hcen1997/pixel-bean/audiuno-code/IMG_20260302_231758.jpg

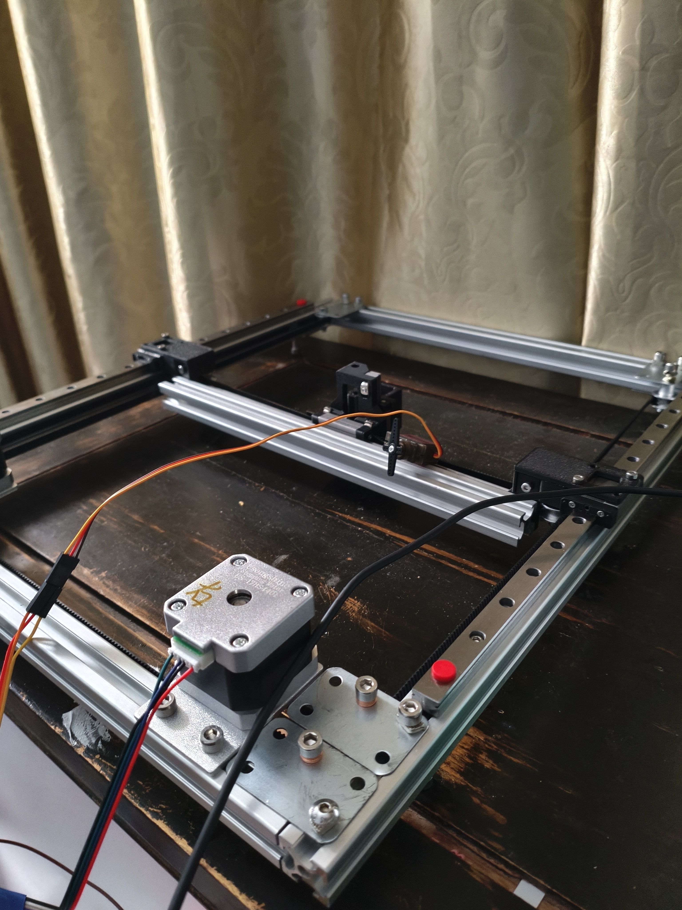
audiuno-code/IMG_20260302_231758.jpg
