hcen1997/pixel-bean/audiuno-code/IMG_20260302_231801.jpg

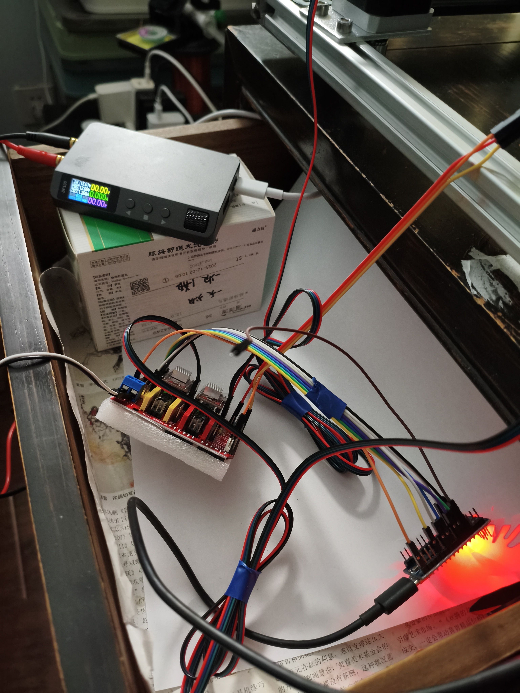
audiuno-code/IMG_20260302_231801.jpg
