hcen1997/pixel-bean/audiuno-code/IMG_20260304_140346.jpg

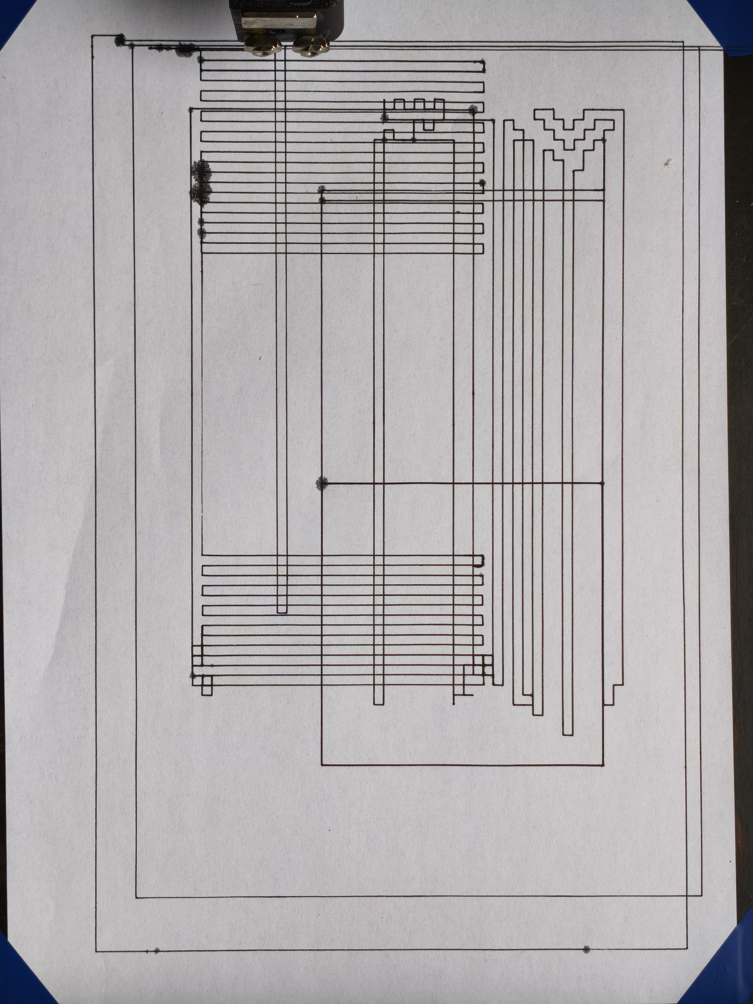
audiuno-code/IMG_20260304_140346.jpg
