hcen1997/pixel-bean/audiuno-code/taobao-doc/c99ceb875f869f8083b27c238d63576b.png

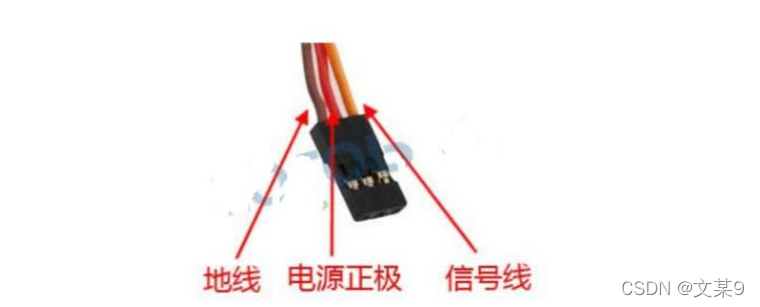
audiuno-code/taobao-doc/c99ceb875f869f8083b27c238d63576b.png
