hcen1997/pixel-bean/audiuno-code/taobao-doc/Screenshot_2026-02-28-11-37-00-495_com.taobao.tao.jpg

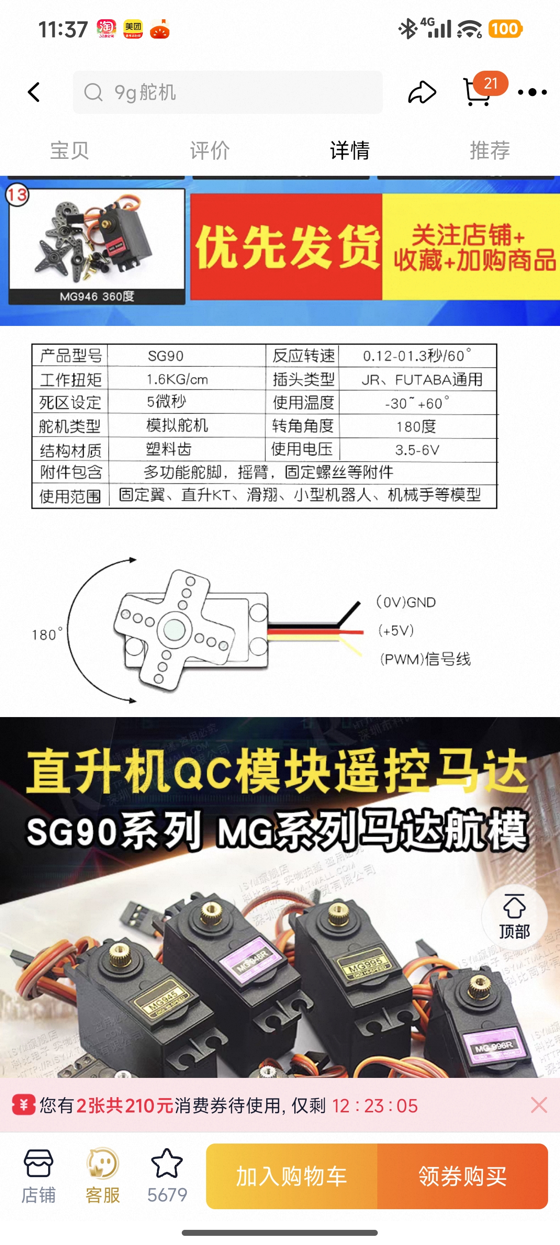
audiuno-code/taobao-doc/Screenshot_2026-02-28-11-37-00-495_com.taobao.tao.jpg
