hcen1997/pixel-bean/audiuno-code/taobao-doc/Screenshot_2026-02-28-11-39-15-636_com.taobao.tao.jpg

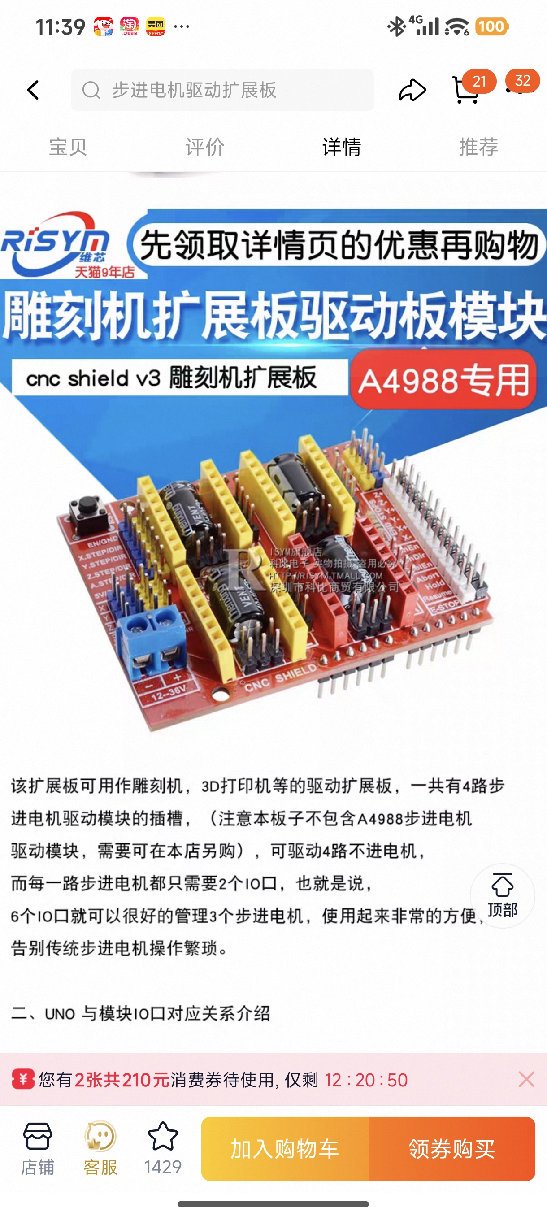
audiuno-code/taobao-doc/Screenshot_2026-02-28-11-39-15-636_com.taobao.tao.jpg
