hcen1997/pixel-bean/audiuno-code/taobao-doc/Screenshot_2026-02-28-11-39-21-068_com.taobao.tao.jpg

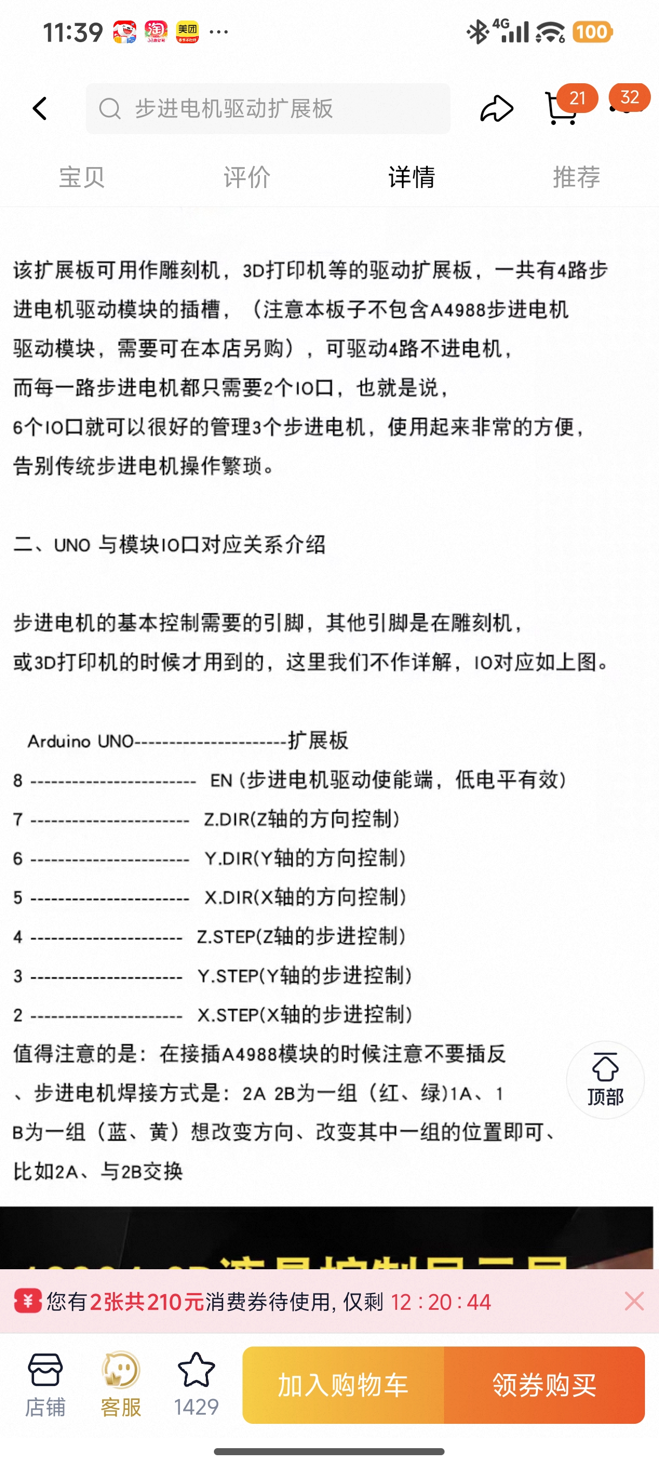
audiuno-code/taobao-doc/Screenshot_2026-02-28-11-39-21-068_com.taobao.tao.jpg
