hcen1997/pixel-bean/grbl-code/0c6dcc0a55ac43939d65316e1c08b687.jpeg~tplv-a9rns2rl98-image.jpg

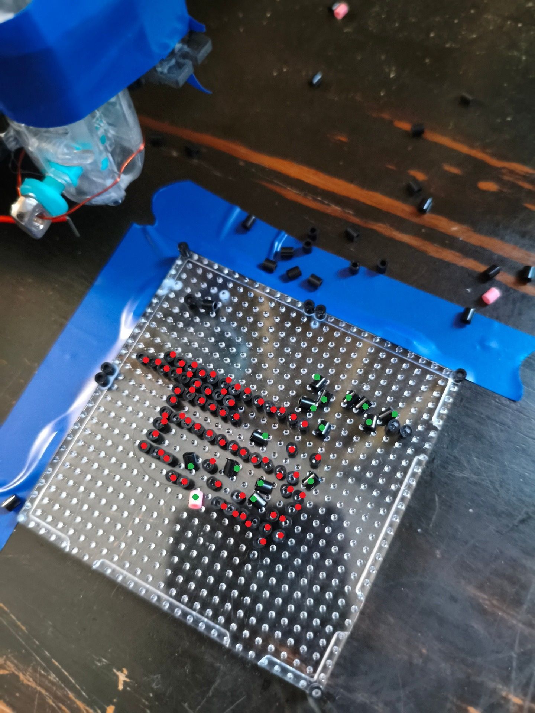
grbl-code/0c6dcc0a55ac43939d65316e1c08b687.jpeg~tplv-a9rns2rl98-image.jpg
