hcen1997/pixel-bean/grbl-code/IMG_20260304_173114.jpg

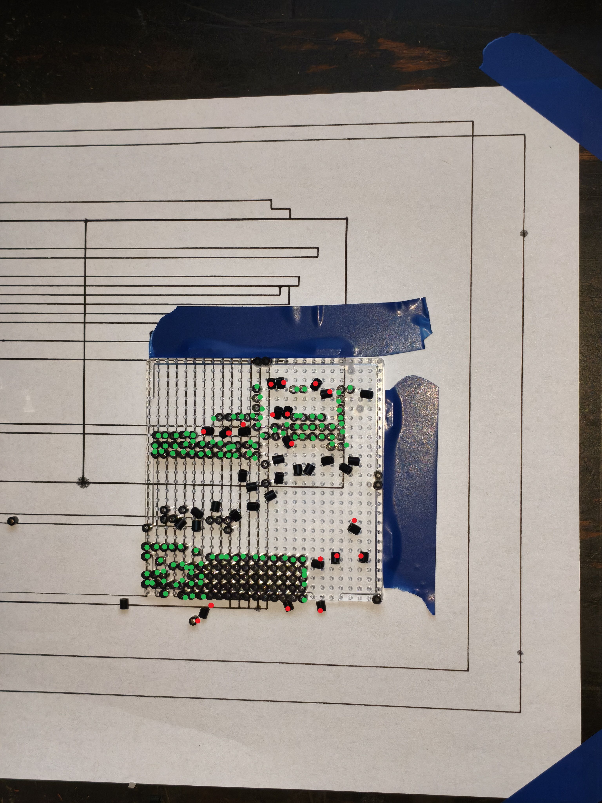
grbl-code/IMG_20260304_173114.jpg
