hcen1997/pixel-bean/grbl-code/pattern-mard-1772532473487.jpg

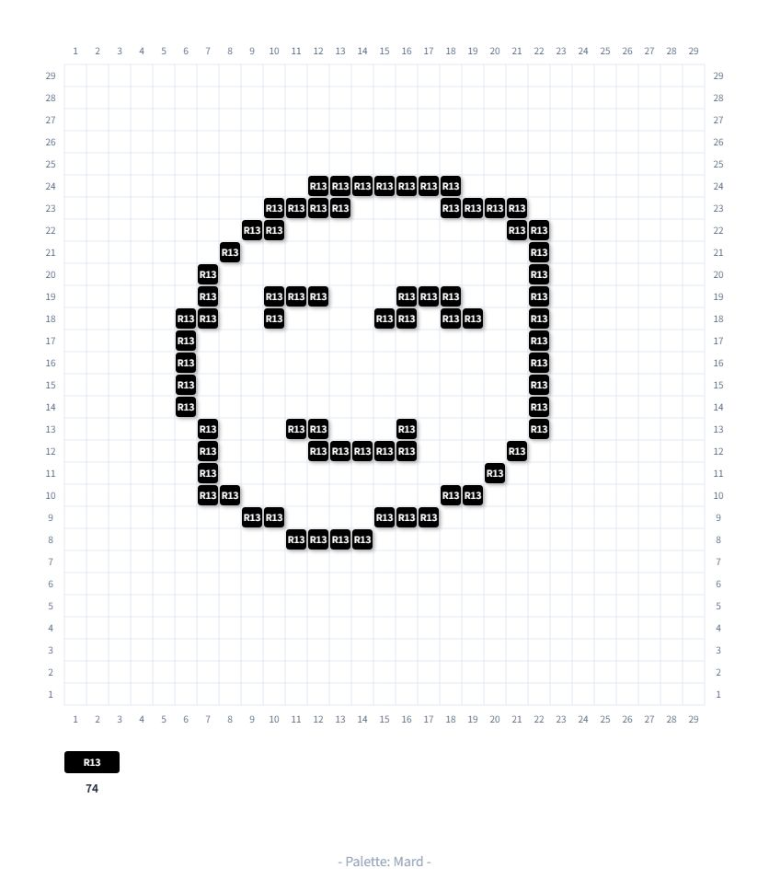
grbl-code/pattern-mard-1772532473487.jpg
