hcen1997/pixel-bean/video_analsys/frames/0001.jpg

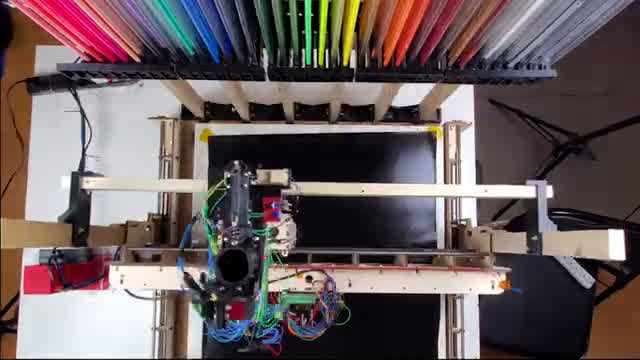
video_analsys/frames/0001.jpg
