hcen1997/pixel-bean/video_analsys/frames/0002.jpg

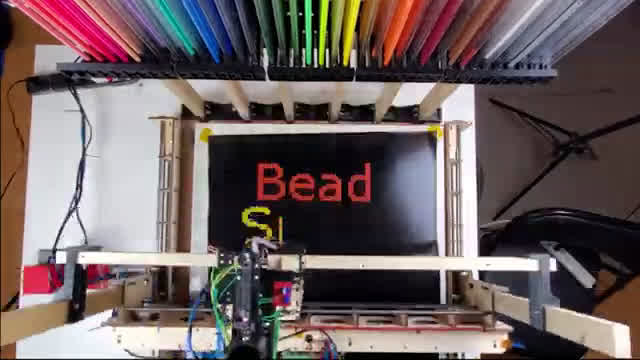
video_analsys/frames/0002.jpg
