hcen1997/pixel-bean/video_analsys/frames/0003.jpg

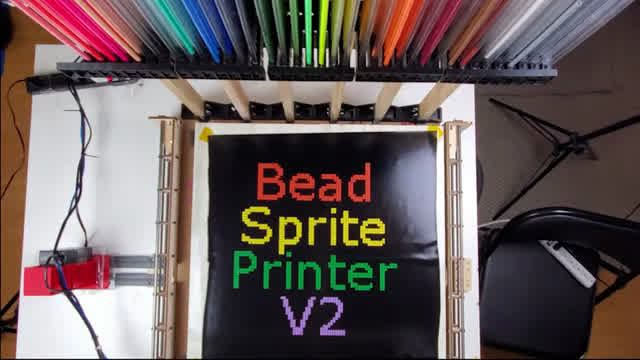
video_analsys/frames/0003.jpg
