hcen1997/pixel-bean/video_analsys/frames/0004.jpg

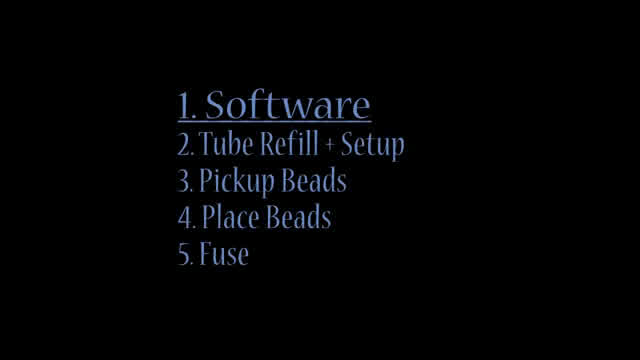
video_analsys/frames/0004.jpg
