hcen1997/pixel-bean/video_analsys/frames/0005.jpg

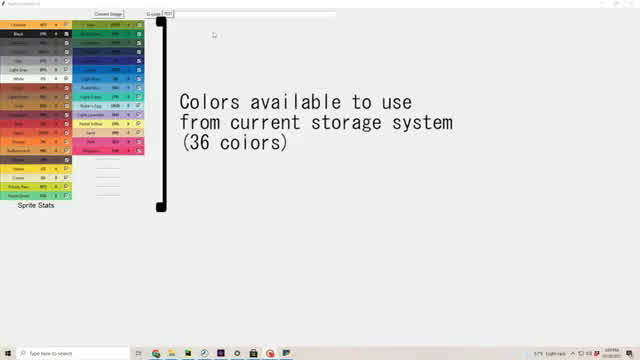
video_analsys/frames/0005.jpg
