hcen1997/pixel-bean/video_analsys/frames/0006.jpg

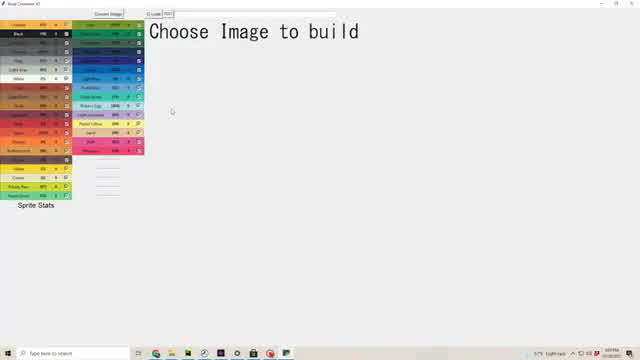
video_analsys/frames/0006.jpg
