hcen1997/pixel-bean/video_analsys/frames/0007.jpg

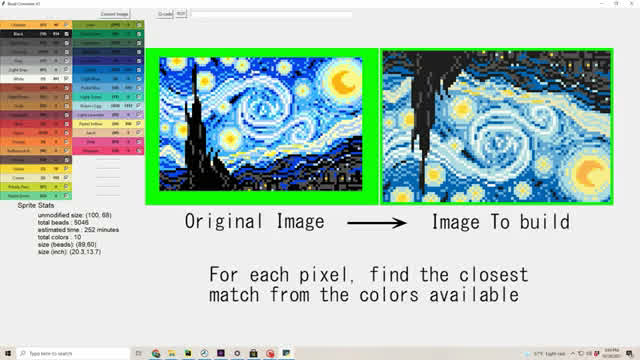
video_analsys/frames/0007.jpg
