hcen1997/pixel-bean/video_analsys/frames/0009.jpg

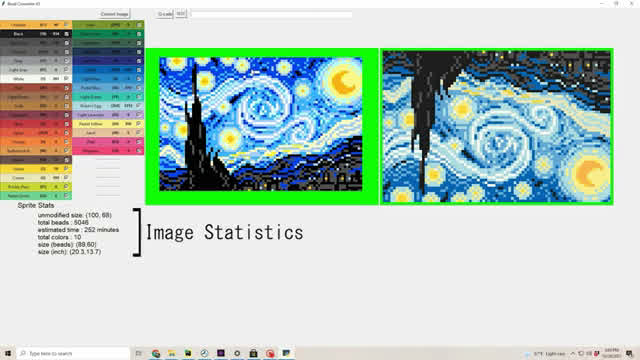
video_analsys/frames/0009.jpg
