hcen1997/pixel-bean/video_analsys/frames/0010.jpg

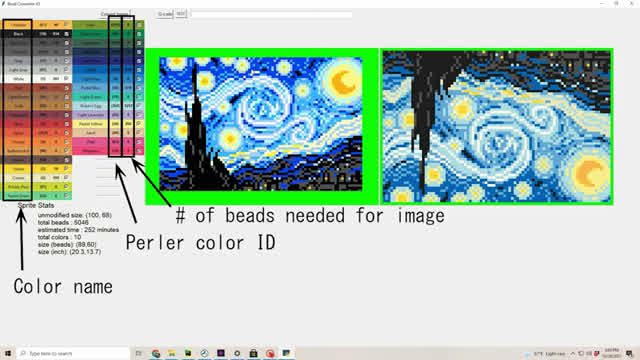
video_analsys/frames/0010.jpg
