hcen1997/pixel-bean/video_analsys/frames/0011.jpg

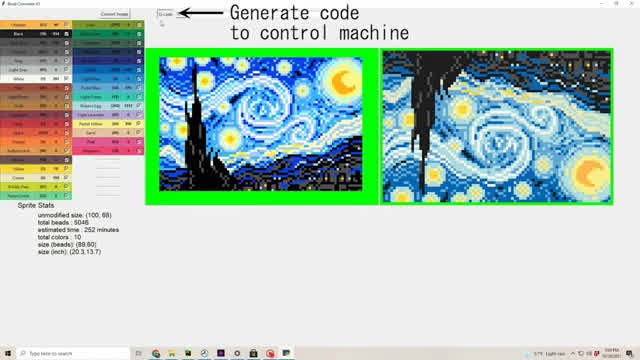
video_analsys/frames/0011.jpg
