hcen1997/pixel-bean/video_analsys/frames/0013.jpg

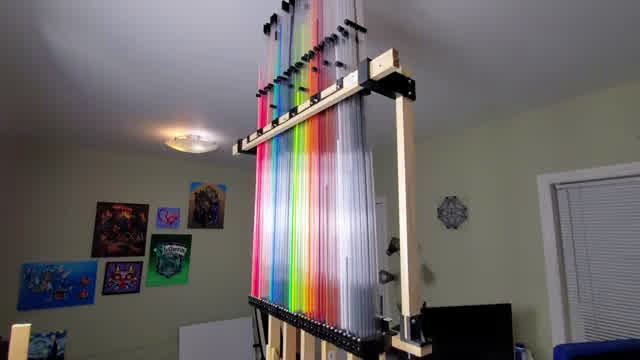
video_analsys/frames/0013.jpg
