hcen1997/pixel-bean/video_analsys/frames/0014.jpg

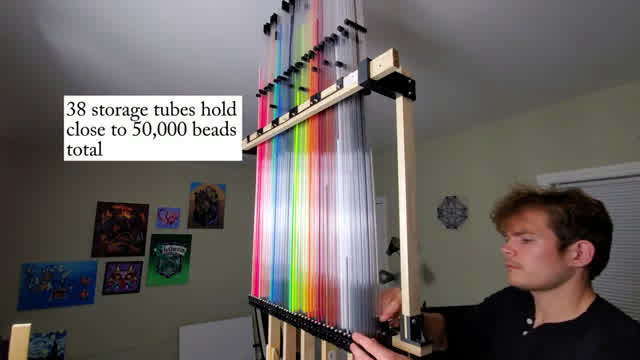
video_analsys/frames/0014.jpg
