hcen1997/pixel-bean/video_analsys/frames/0015.jpg

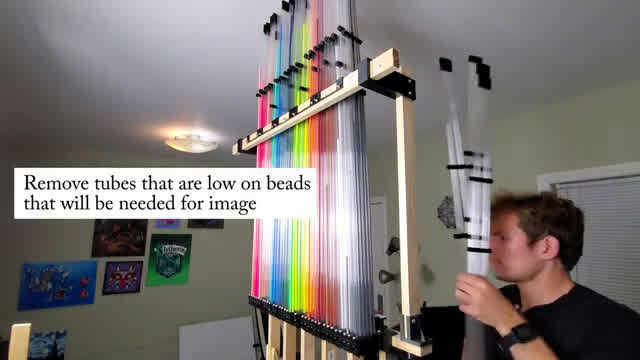
video_analsys/frames/0015.jpg
