hcen1997/pixel-bean/video_analsys/frames/0016.jpg

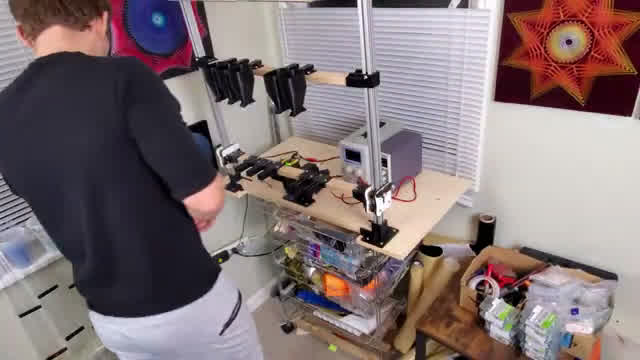
video_analsys/frames/0016.jpg
