hcen1997/pixel-bean/video_analsys/frames/0017.jpg

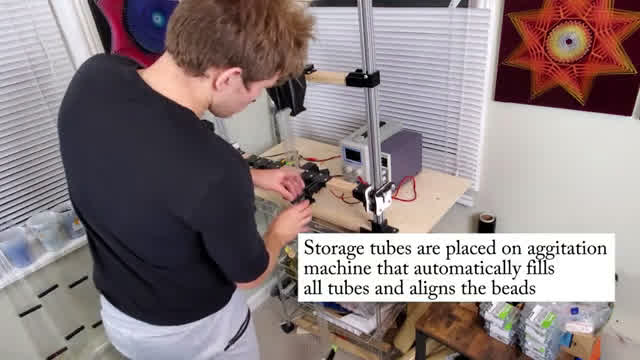
video_analsys/frames/0017.jpg
