hcen1997/pixel-bean/video_analsys/frames/0018.jpg

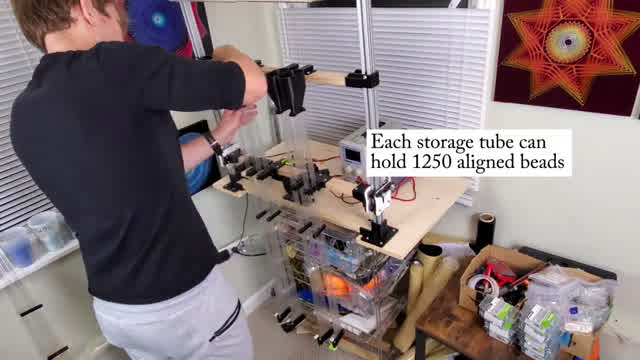
video_analsys/frames/0018.jpg
