hcen1997/pixel-bean/video_analsys/frames/0019.jpg

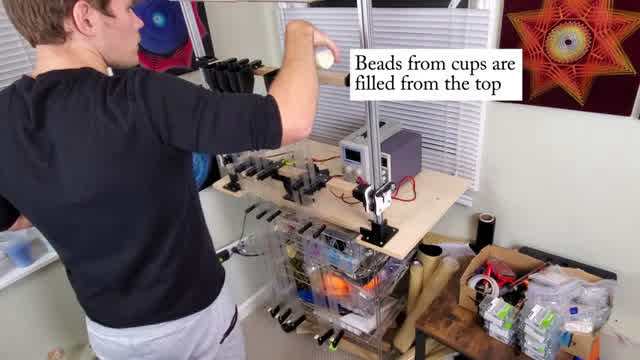
video_analsys/frames/0019.jpg
