hcen1997/pixel-bean/video_analsys/frames/0020.jpg

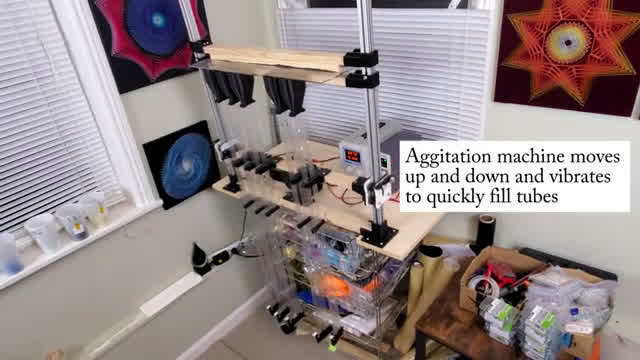
video_analsys/frames/0020.jpg
