hcen1997/pixel-bean/video_analsys/frames/0021.jpg

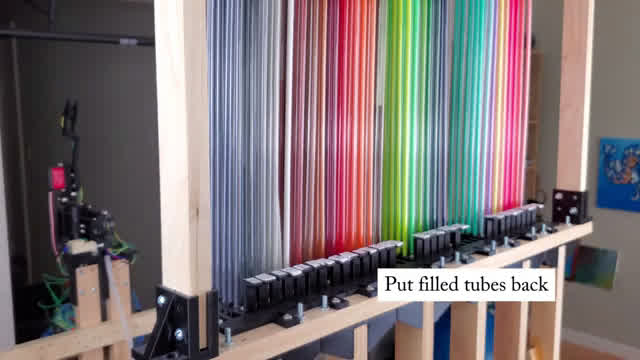
video_analsys/frames/0021.jpg
