hcen1997/pixel-bean/video_analsys/frames/0022.jpg

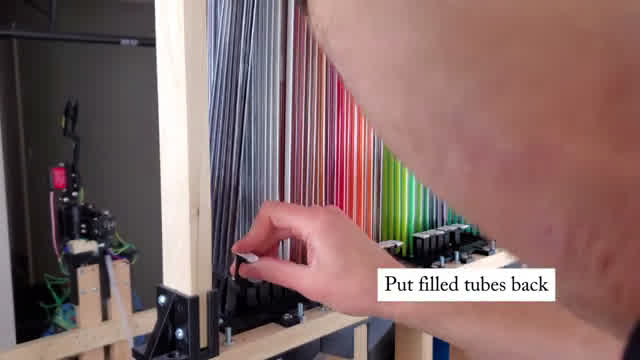
video_analsys/frames/0022.jpg
