hcen1997/pixel-bean/video_analsys/frames/0024.jpg

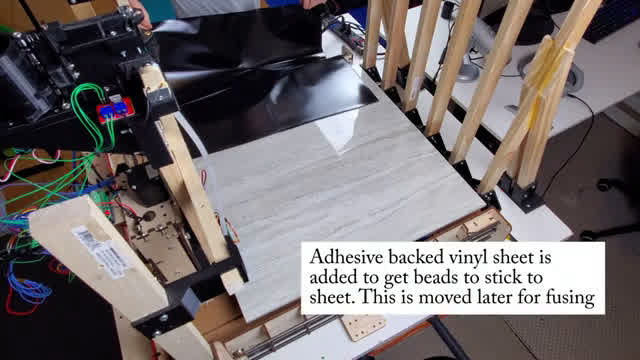
video_analsys/frames/0024.jpg
