hcen1997/pixel-bean/video_analsys/frames/0026.jpg

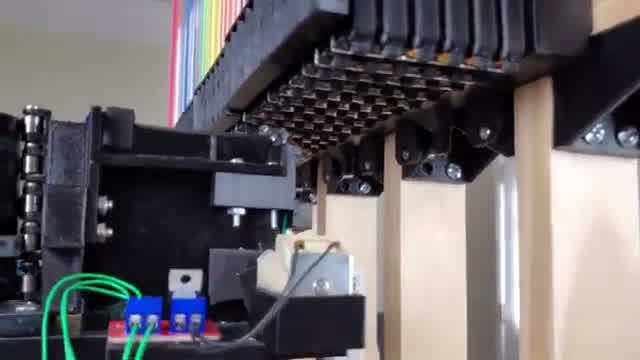
video_analsys/frames/0026.jpg
