hcen1997/pixel-bean/video_analsys/frames/0027.jpg

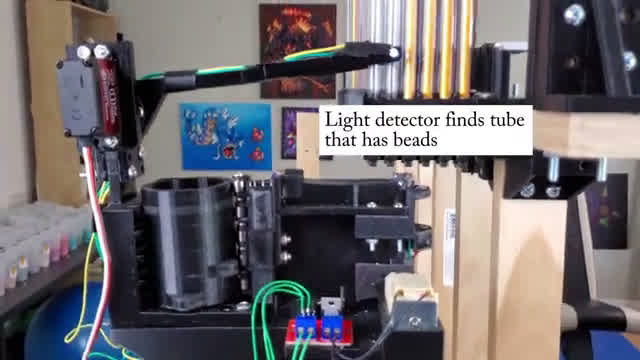
video_analsys/frames/0027.jpg
