hcen1997/pixel-bean/video_analsys/frames/0028.jpg

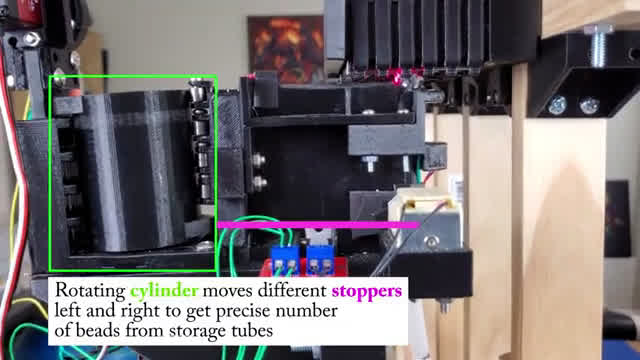
video_analsys/frames/0028.jpg
