hcen1997/pixel-bean/video_analsys/frames/0029.jpg

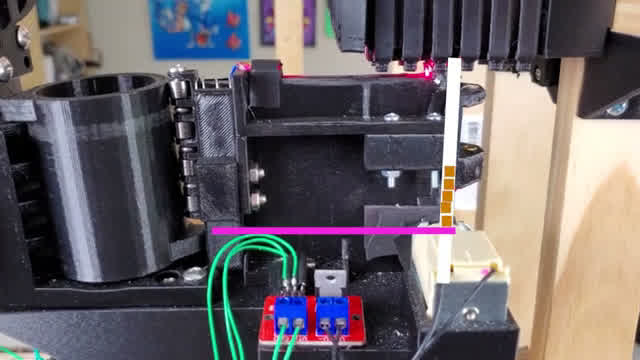
video_analsys/frames/0029.jpg
