hcen1997/pixel-bean/video_analsys/frames/0030.jpg

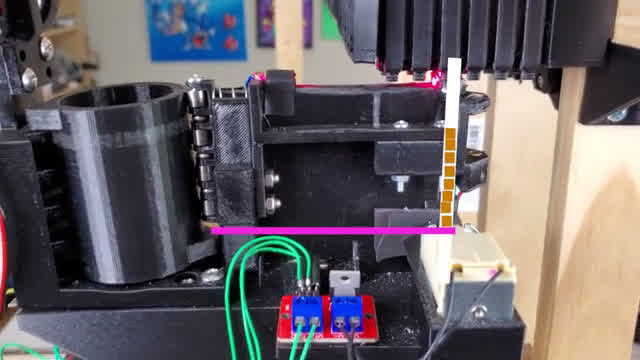
video_analsys/frames/0030.jpg
