hcen1997/pixel-bean/video_analsys/frames/0031.jpg

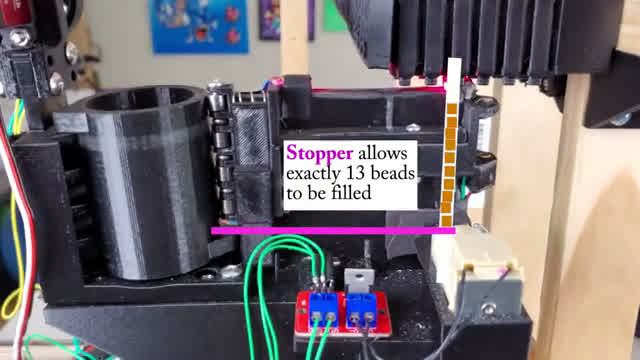
video_analsys/frames/0031.jpg
