hcen1997/pixel-bean/video_analsys/frames/0032.jpg

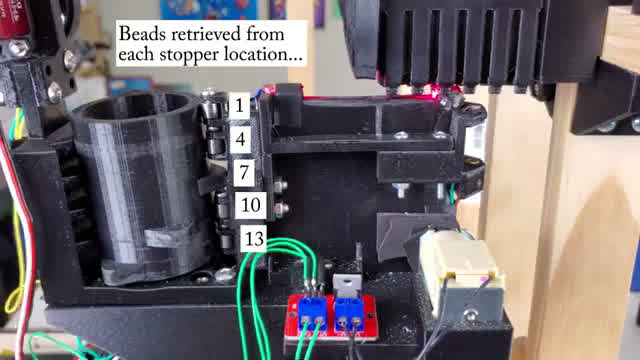
video_analsys/frames/0032.jpg
