hcen1997/pixel-bean/video_analsys/frames/0033.jpg

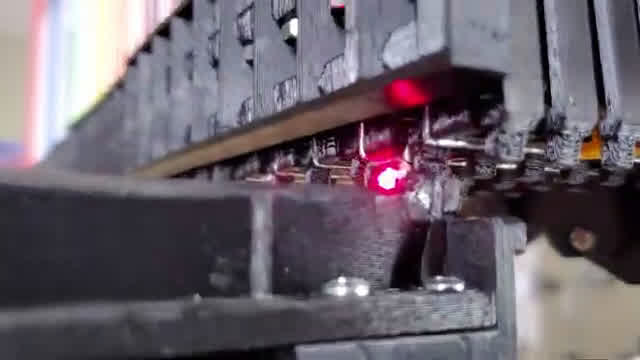
video_analsys/frames/0033.jpg
