hcen1997/pixel-bean/video_analsys/frames/0034.jpg

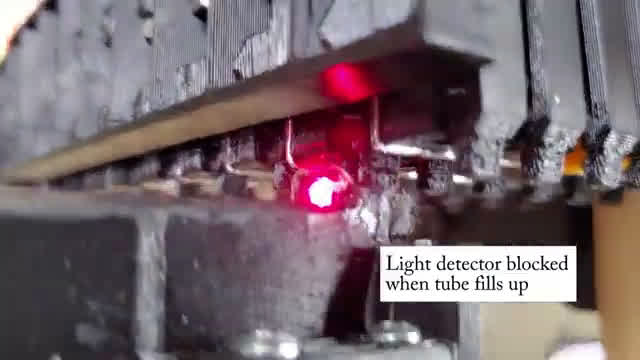
video_analsys/frames/0034.jpg
