hcen1997/pixel-bean/video_analsys/frames/0035.jpg

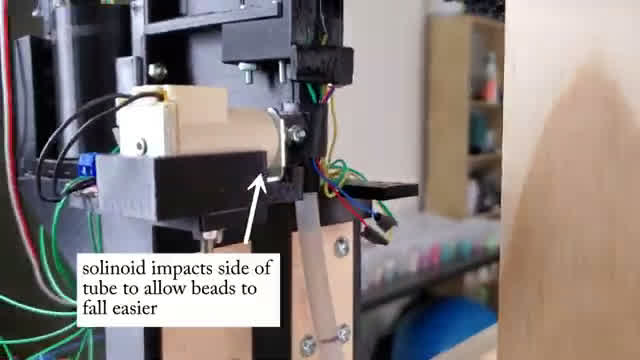
video_analsys/frames/0035.jpg
