hcen1997/pixel-bean/video_analsys/frames/0037.jpg

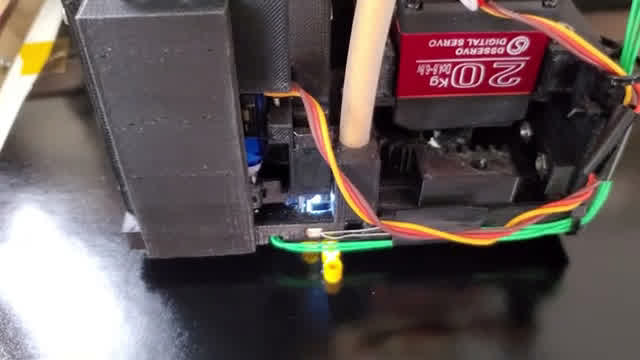
video_analsys/frames/0037.jpg
