hcen1997/pixel-bean/video_analsys/frames/0038.jpg

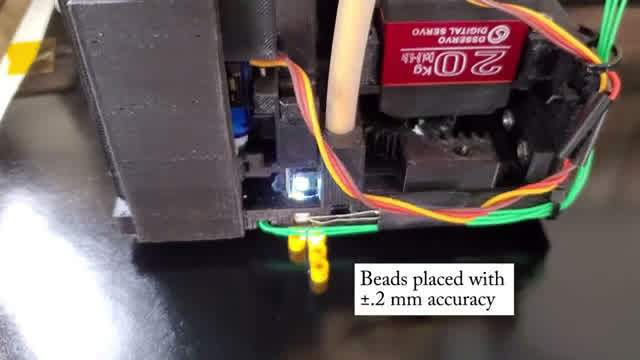
video_analsys/frames/0038.jpg
