hcen1997/pixel-bean/video_analsys/frames/0039.jpg

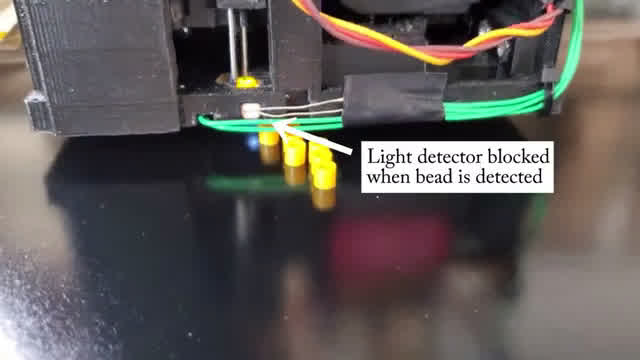
video_analsys/frames/0039.jpg
