hcen1997/pixel-bean/video_analsys/frames/0040.jpg

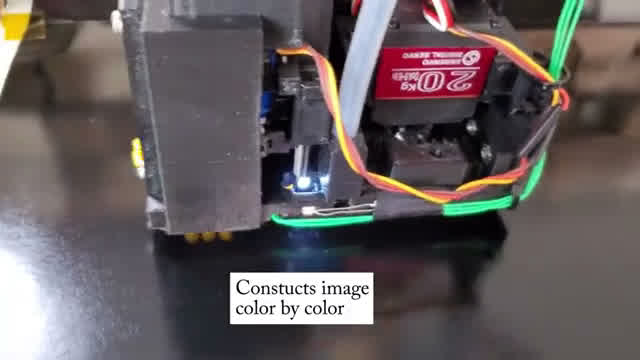
video_analsys/frames/0040.jpg
