hcen1997/pixel-bean/video_analsys/frames/0041.jpg

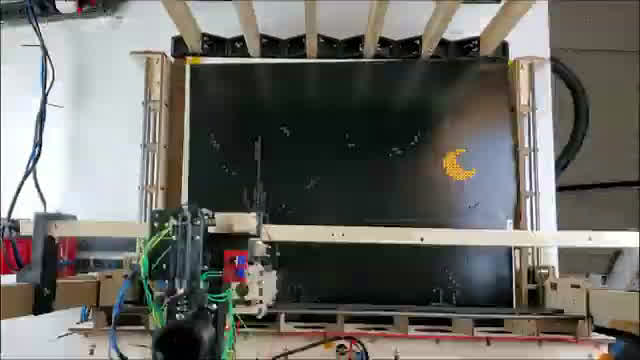
video_analsys/frames/0041.jpg
