hcen1997/pixel-bean/video_analsys/frames/0042.jpg

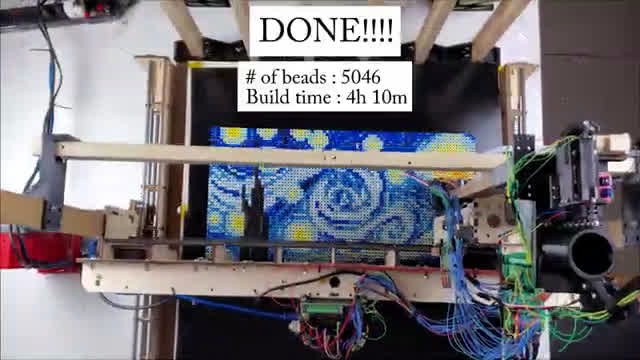
video_analsys/frames/0042.jpg
