hcen1997/pixel-bean/video_analsys/frames/0043.jpg

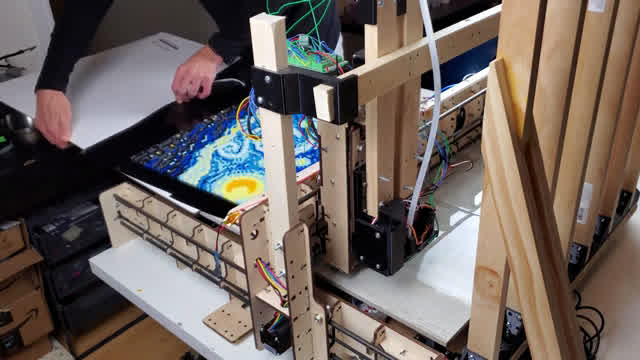
video_analsys/frames/0043.jpg
