hcen1997/pixel-bean/video_analsys/frames/0044.jpg

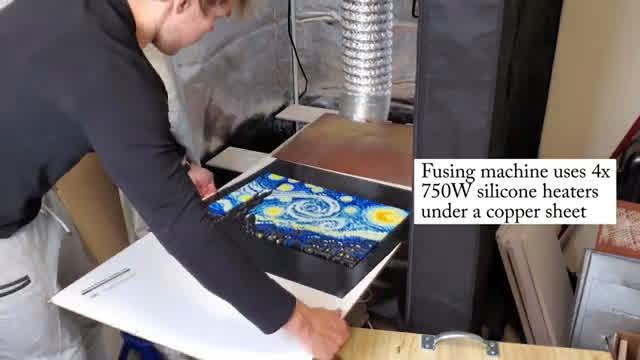
video_analsys/frames/0044.jpg
