hcen1997/pixel-bean/video_analsys/frames/0045.jpg

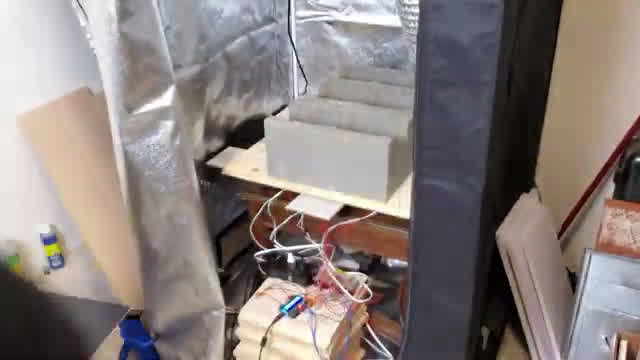
video_analsys/frames/0045.jpg
