hcen1997/pixel-bean/video_analsys/frames/0046.jpg

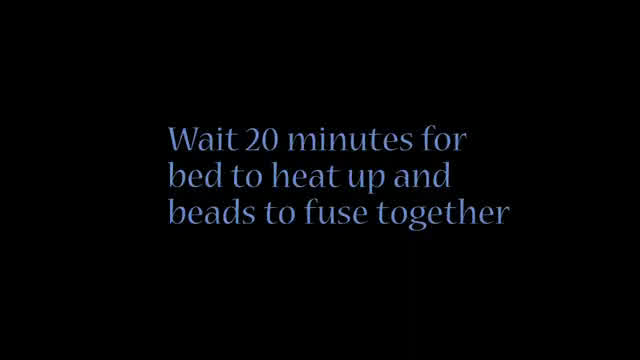
video_analsys/frames/0046.jpg
