hcen1997/pixel-bean/video_analsys/frames/0047.jpg

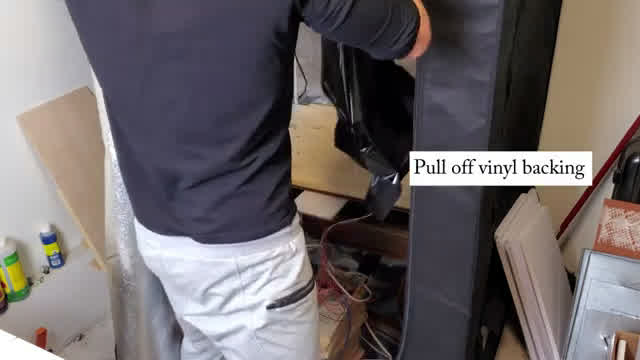
video_analsys/frames/0047.jpg
