hcen1997/pixel-bean/video_analsys/frames/0048.jpg

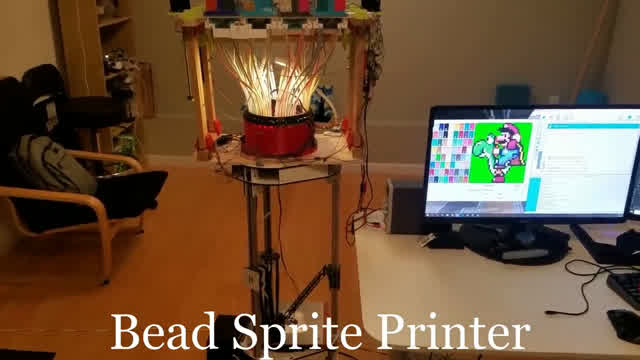
video_analsys/frames/0048.jpg
