hcen1997/pixel-bean/video_analsys/frames/0049.jpg

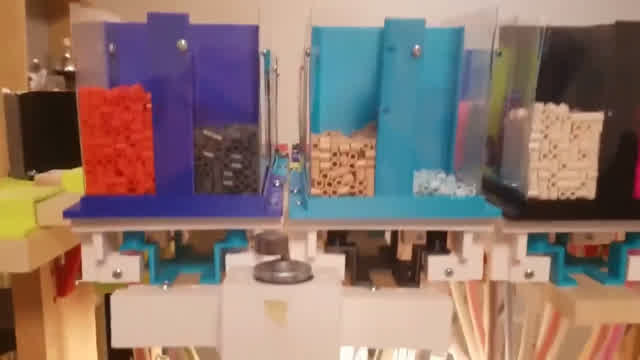
video_analsys/frames/0049.jpg
