hcen1997/pixel-bean/video_analsys/frames/0050.jpg

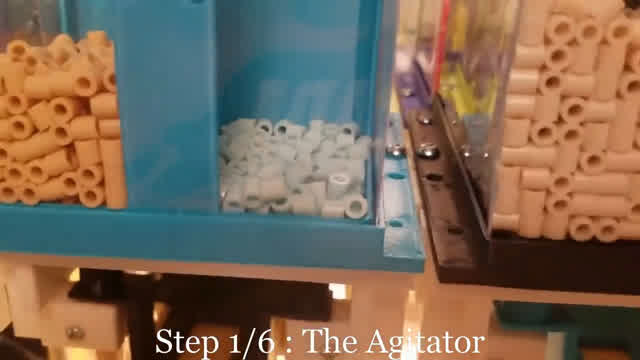
video_analsys/frames/0050.jpg
