hcen1997/pixel-bean/video_analsys/frames/0051.jpg

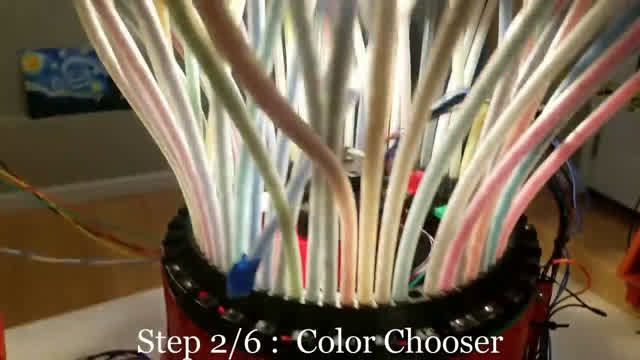
video_analsys/frames/0051.jpg
