hcen1997/pixel-bean/video_analsys/frames/0052.jpg

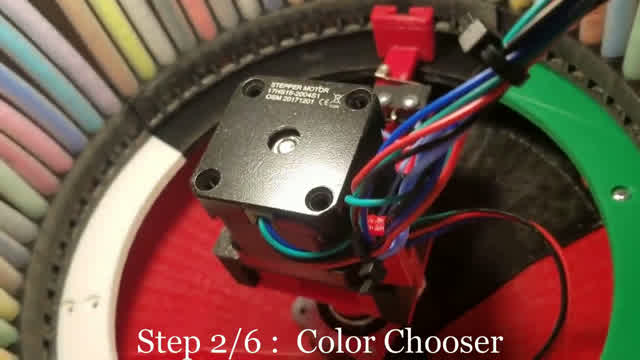
video_analsys/frames/0052.jpg
