hcen1997/pixel-bean/video_analsys/frames/0053.jpg

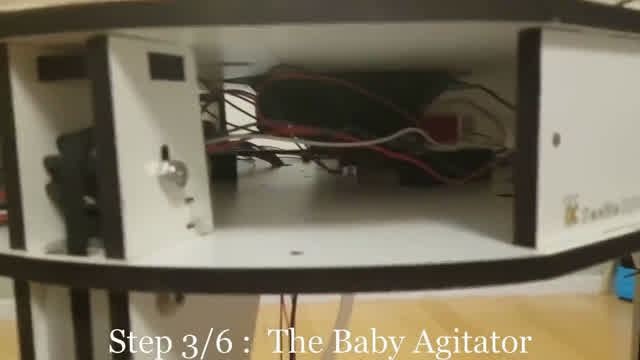
video_analsys/frames/0053.jpg
