hcen1997/pixel-bean/video_analsys/frames/0054.jpg

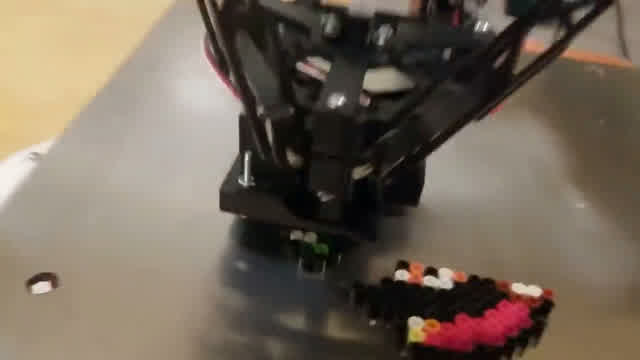
video_analsys/frames/0054.jpg
