hcen1997/pixel-bean/video_analsys/frames/0055.jpg

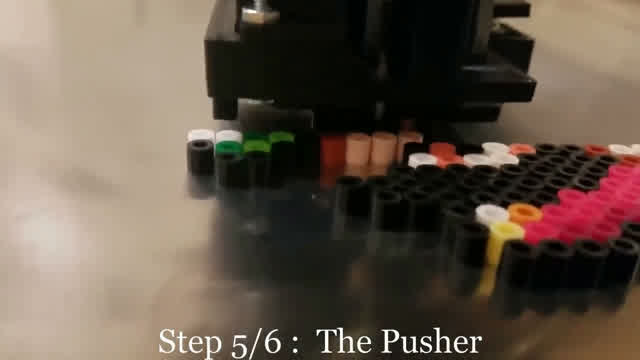
video_analsys/frames/0055.jpg
