hcen1997/pixel-bean/video_analsys/frames/0056.jpg

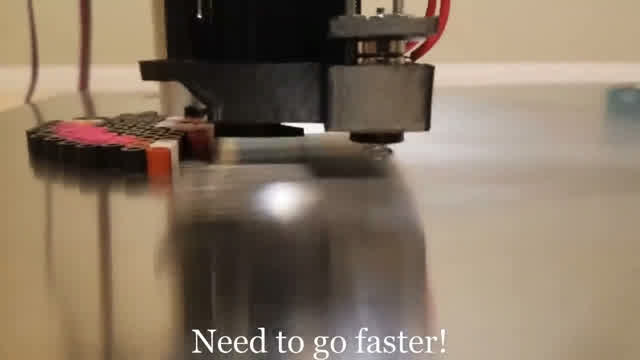
video_analsys/frames/0056.jpg
