hcen1997/pixel-bean/video_analsys/frames/0057.jpg

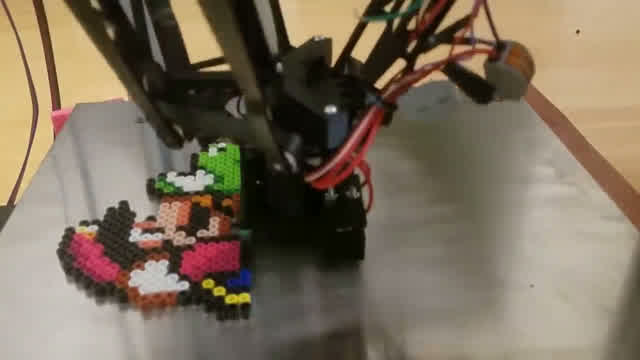
video_analsys/frames/0057.jpg
