hcen1997/pixel-bean/video_analsys/frames/0058.jpg

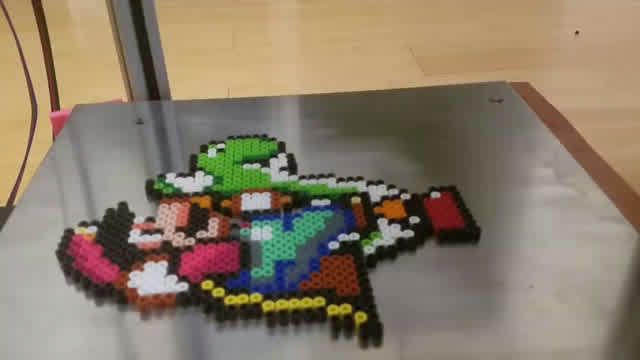
video_analsys/frames/0058.jpg
