hcen1997/pixel-bean/video_analsys/frames/0060.jpg

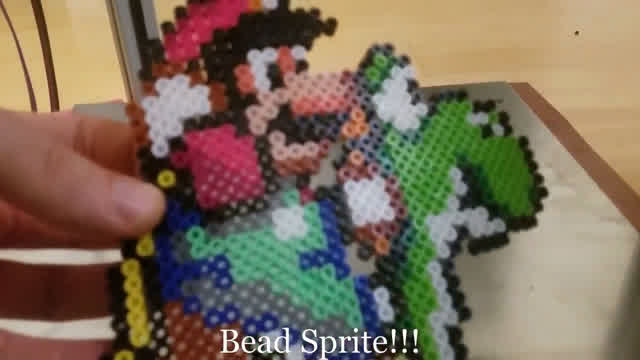
video_analsys/frames/0060.jpg
