hcen1997/pixel-bean/video_analsys/frames/0061.jpg

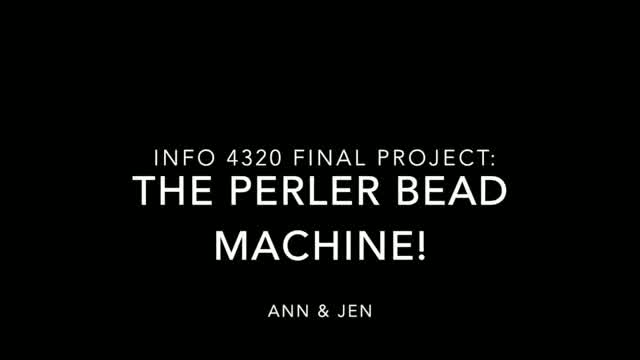
video_analsys/frames/0061.jpg
