hcen1997/pixel-bean/video_analsys/frames/0062.jpg

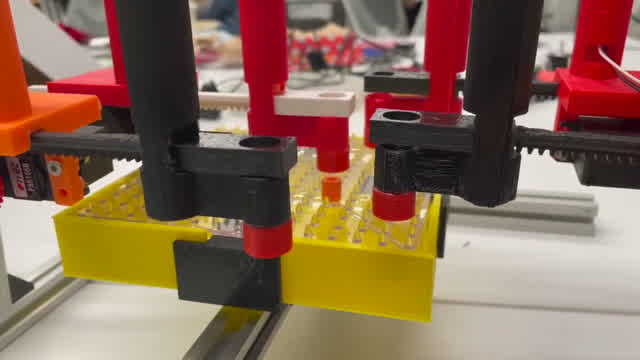
video_analsys/frames/0062.jpg
