hcen1997/pixel-bean/video_analsys/frames/0063.jpg

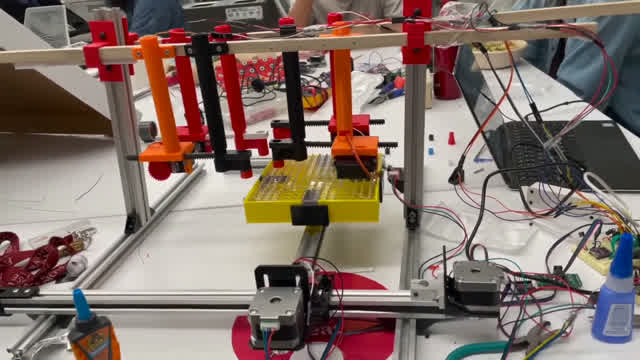
video_analsys/frames/0063.jpg
