hcen1997/pixel-bean/video_analsys/frames/0064.jpg

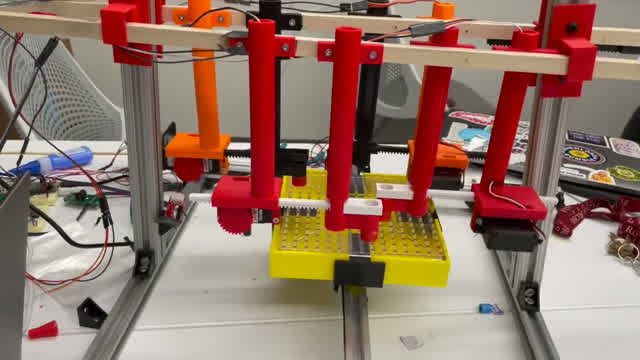
video_analsys/frames/0064.jpg
