hcen1997/pixel-bean/video_analsys/frames/0065.jpg

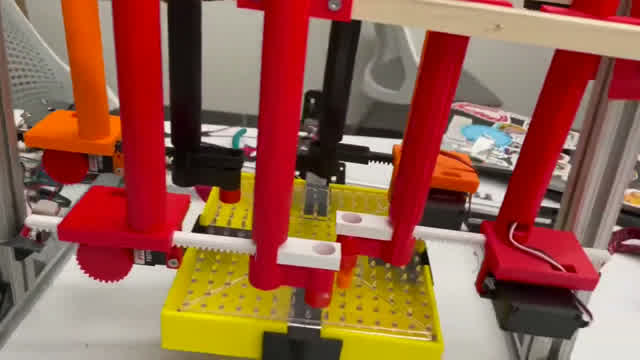
video_analsys/frames/0065.jpg
