hcen1997/pixel-bean/video_analsys/frames/0067.jpg

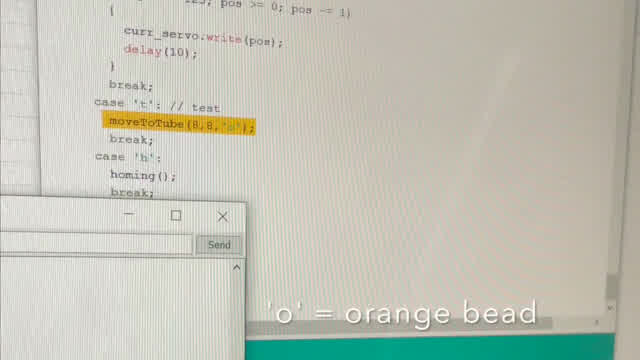
video_analsys/frames/0067.jpg
