hcen1997/pixel-bean/video_analsys/frames/0068.jpg

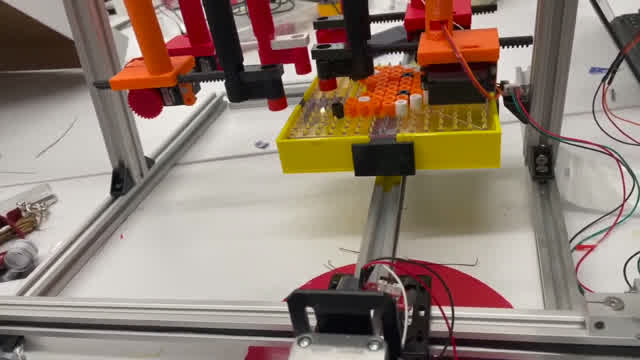
video_analsys/frames/0068.jpg
