hcen1997/pixel-bean/video_analsys/frames/0069.jpg

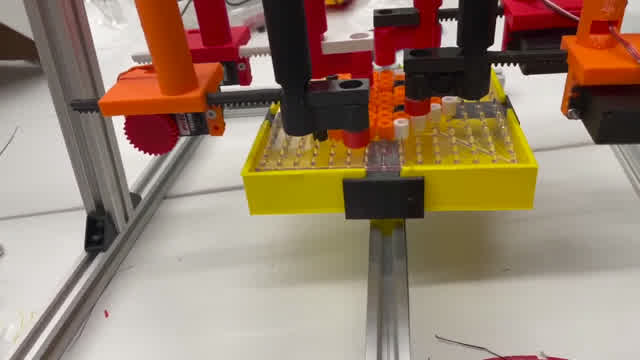
video_analsys/frames/0069.jpg
