hcen1997/pixel-bean/video_analsys/frames/0070.jpg

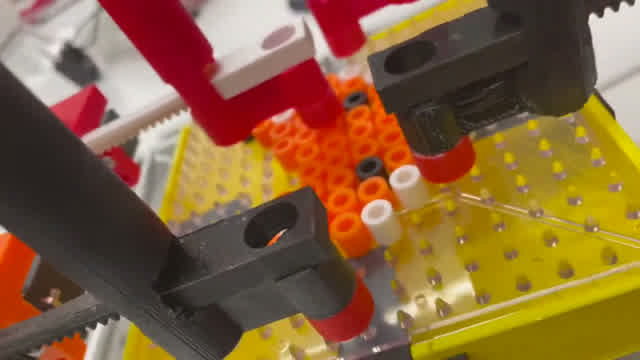
video_analsys/frames/0070.jpg
