hcen1997/pixel-bean/video_analsys/frames/0071.jpg

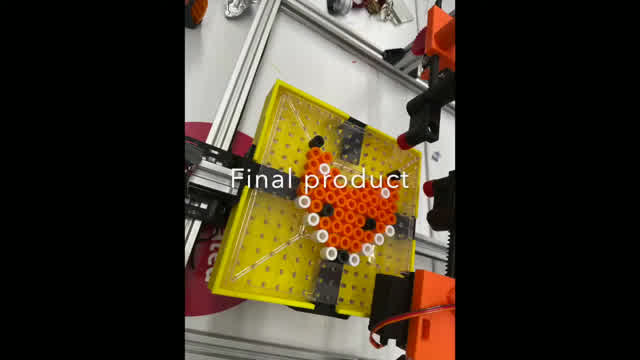
video_analsys/frames/0071.jpg
