hcen1997/pixel-bean/video_analsys/frames/0072.jpg

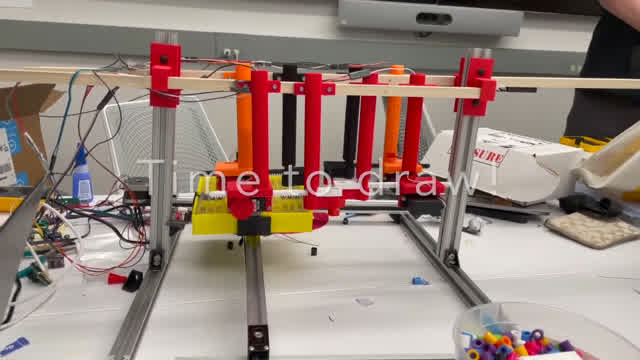
video_analsys/frames/0072.jpg
