hcen1997/pixel-bean/video_analsys/frames/0073.jpg

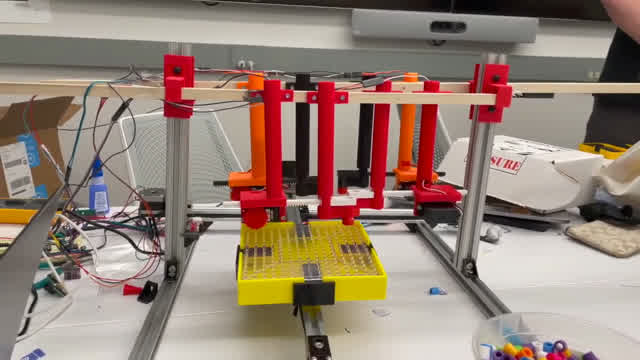
video_analsys/frames/0073.jpg
