hcen1997/pixel-bean/video_analsys/frames/0074.jpg

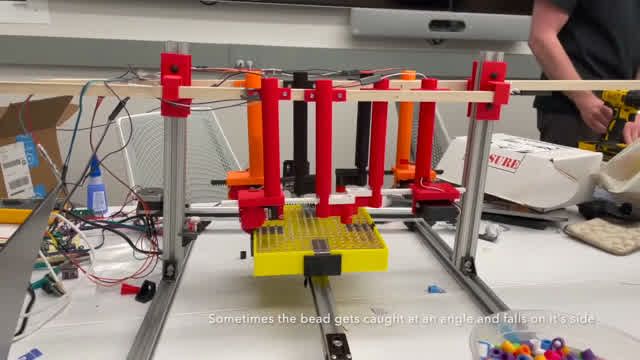
video_analsys/frames/0074.jpg
