hcen1997/pixel-bean/video_analsys/frames/0075.jpg

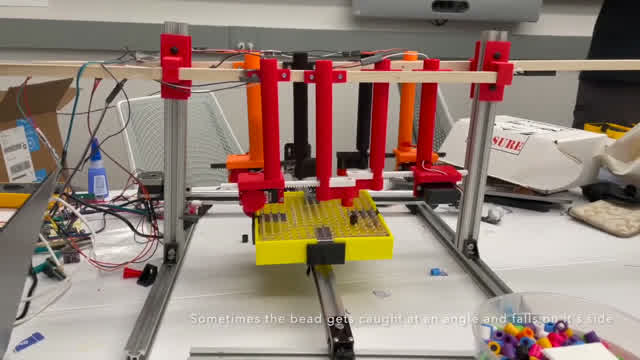
video_analsys/frames/0075.jpg
