hcen1997/pixel-bean/video_analsys/frames/0076.jpg

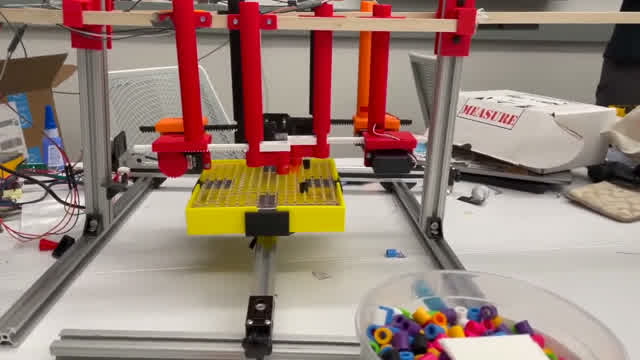
video_analsys/frames/0076.jpg
