hcen1997/pixel-bean/video_analsys/frames/0077.jpg

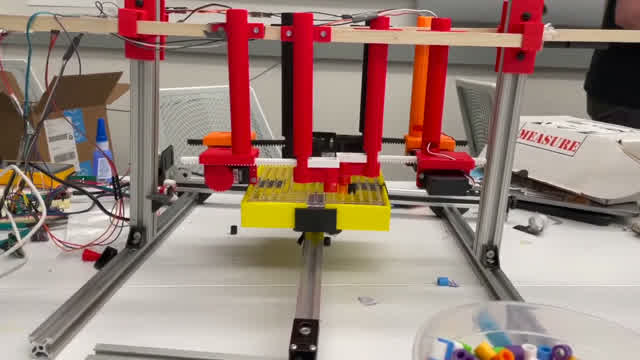
video_analsys/frames/0077.jpg
