hcen1997/pixel-bean/video_analsys/frames/0078.jpg

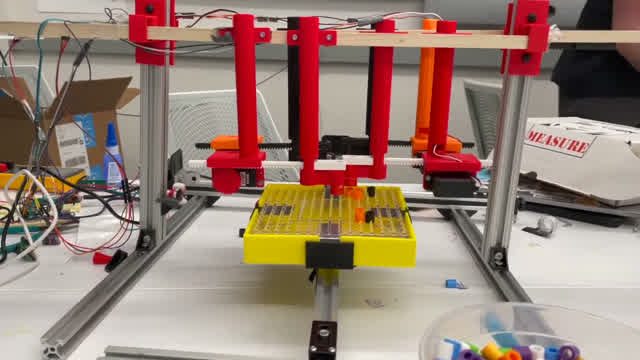
video_analsys/frames/0078.jpg
