hcen1997/pixel-bean/video_analsys/frames/0079.jpg

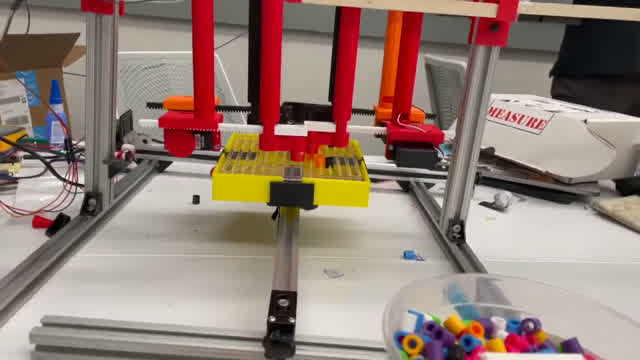
video_analsys/frames/0079.jpg
