hcen1997/pixel-bean/video_analsys/frames/0080.jpg

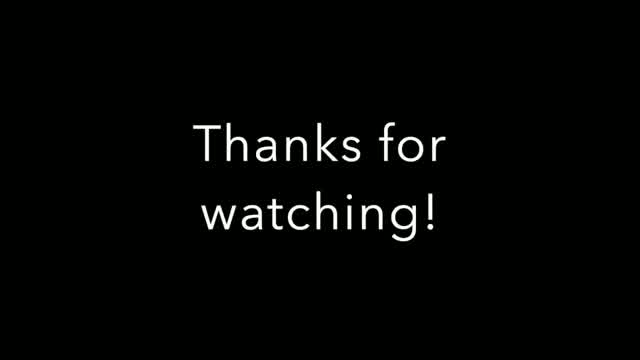
video_analsys/frames/0080.jpg
