hcen1997/pixel-bean/video_analsys/frames/0081.jpg

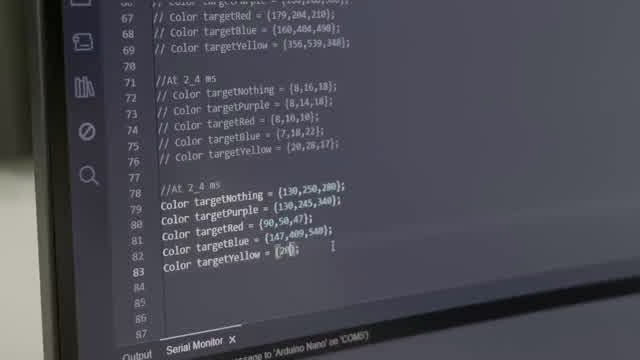
video_analsys/frames/0081.jpg
