hcen1997/pixel-bean/video_analsys/frames/0082.jpg

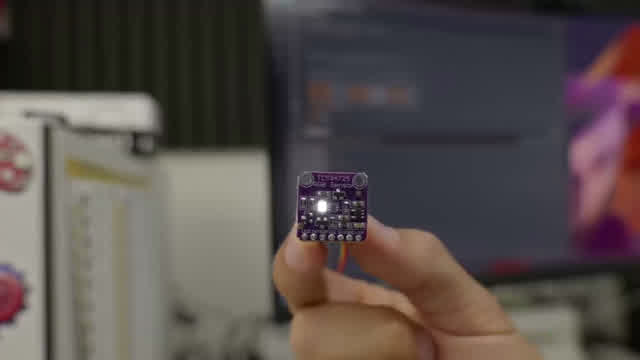
video_analsys/frames/0082.jpg
