hcen1997/pixel-bean/video_analsys/frames/0083.jpg

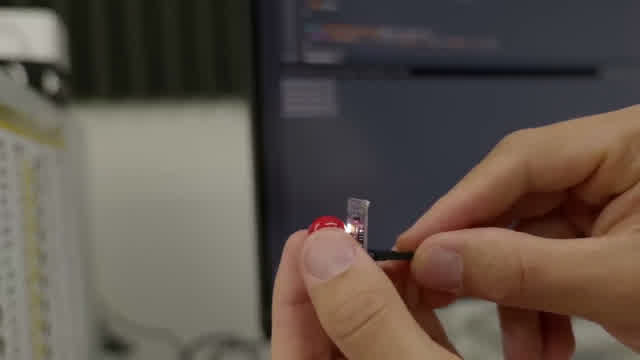
video_analsys/frames/0083.jpg
