hcen1997/pixel-bean/video_analsys/frames/0084.jpg

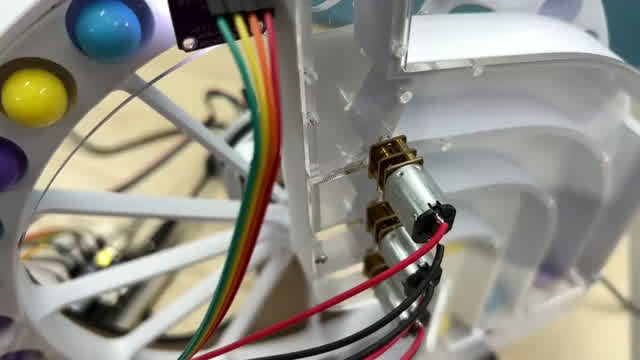
video_analsys/frames/0084.jpg
