hcen1997/pixel-bean/video_analsys/frames/0085.jpg

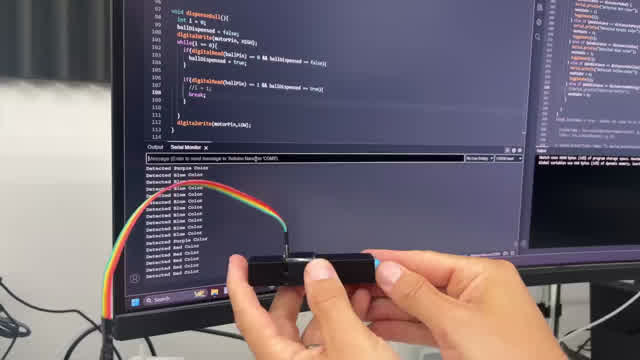
video_analsys/frames/0085.jpg
