hcen1997/pixel-bean/video_analsys/frames/0086.jpg

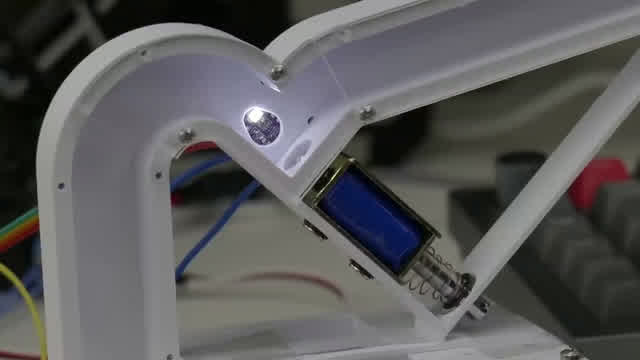
video_analsys/frames/0086.jpg
