hcen1997/pixel-bean/video_analsys/frames/0087.jpg

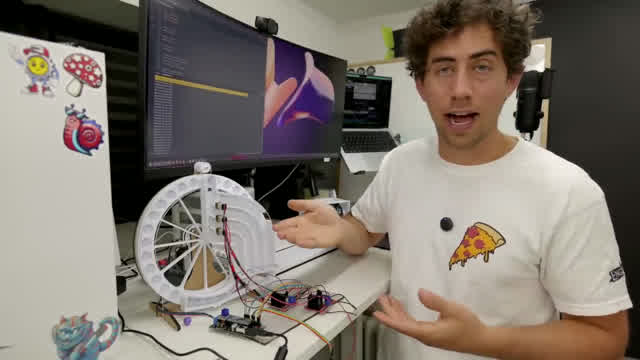
video_analsys/frames/0087.jpg
