hcen1997/pixel-bean/video_analsys/frames/0088.jpg

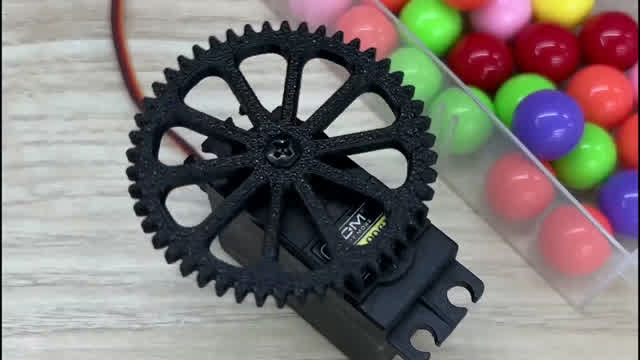
video_analsys/frames/0088.jpg
