hcen1997/pixel-bean/video_analsys/frames/0089.jpg

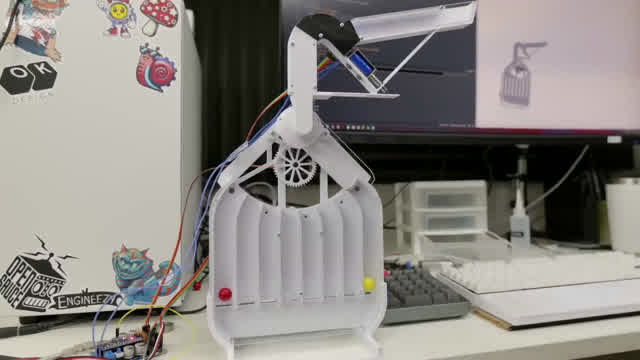
video_analsys/frames/0089.jpg
