hcen1997/pixel-bean/video_analsys/frames/0090.jpg

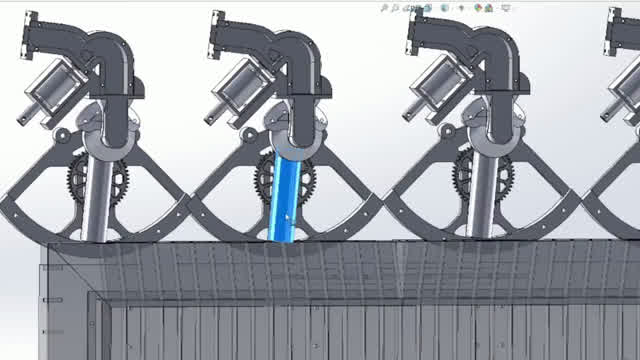
video_analsys/frames/0090.jpg
