hcen1997/pixel-bean/video_analsys/frames/0091.jpg

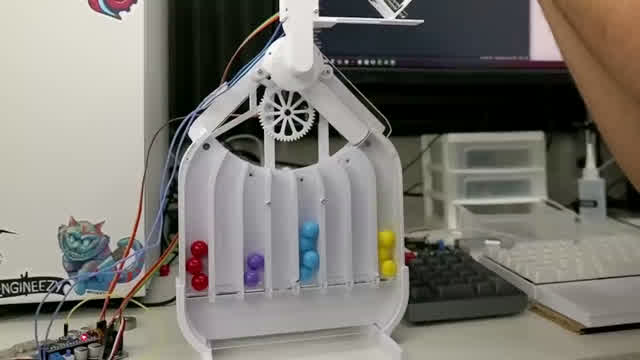
video_analsys/frames/0091.jpg
