hcen1997/pixel-bean/video_analsys/frames/0092.jpg

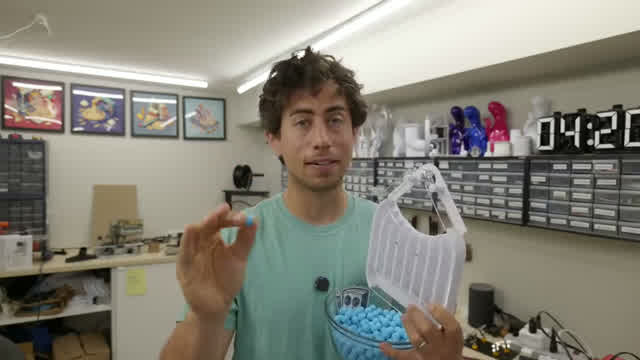
video_analsys/frames/0092.jpg
