hcen1997/pixel-bean/video_analsys/frames/0093.jpg

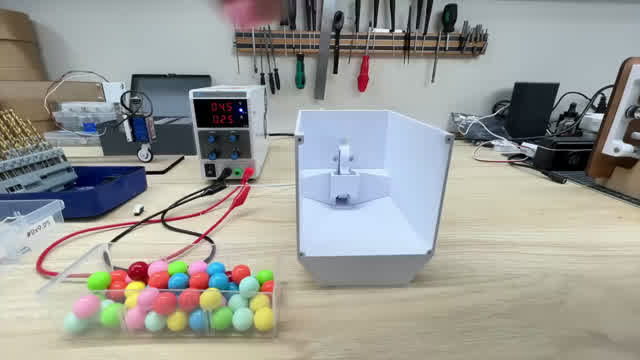
video_analsys/frames/0093.jpg
