hcen1997/pixel-bean/video_analsys/frames/0094.jpg

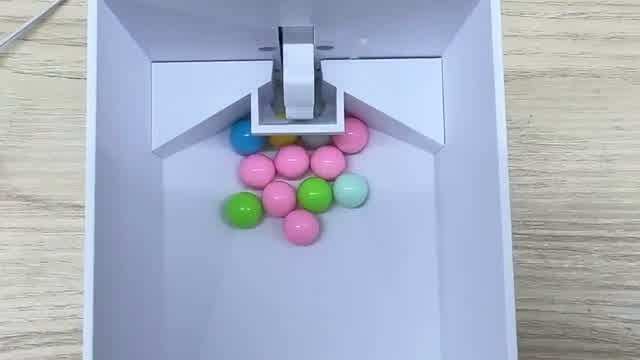
video_analsys/frames/0094.jpg
