hcen1997/pixel-bean/video_analsys/frames/0095.jpg

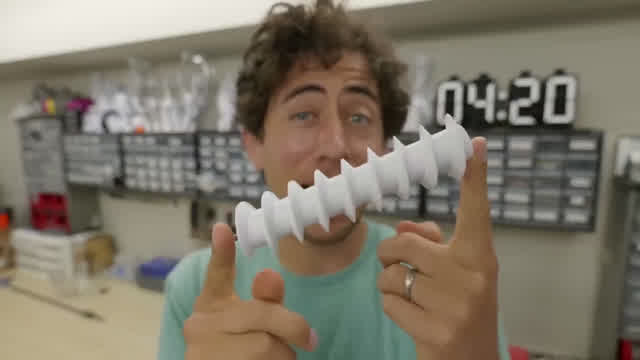
video_analsys/frames/0095.jpg
