hcen1997/pixel-bean/video_analsys/frames/0096.jpg

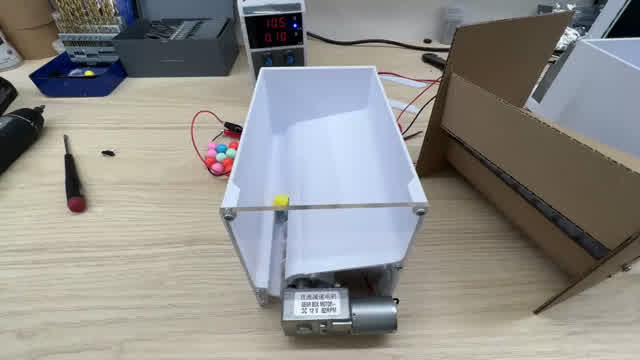
video_analsys/frames/0096.jpg
