hcen1997/pixel-bean/video_analsys/frames/0097.jpg

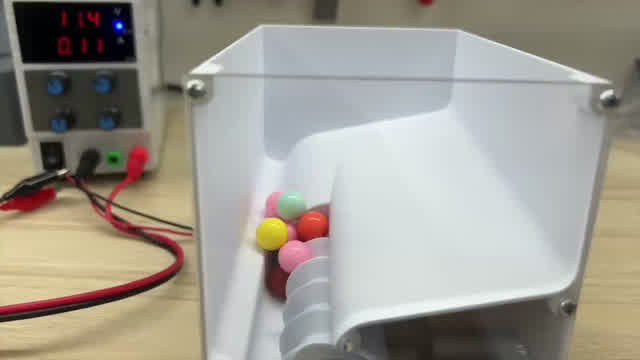
video_analsys/frames/0097.jpg
