hcen1997/pixel-bean/video_analsys/frames/0098.jpg

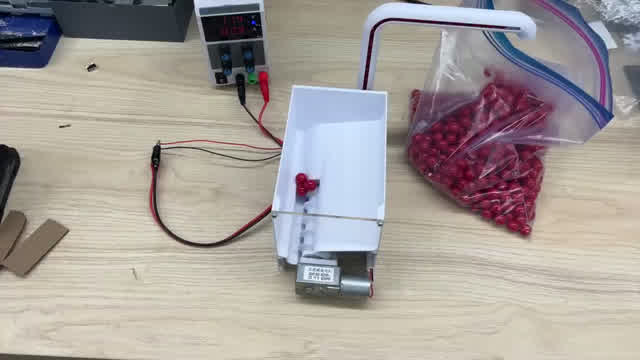
video_analsys/frames/0098.jpg
