hcen1997/pixel-bean/video_analsys/frames/0099.jpg

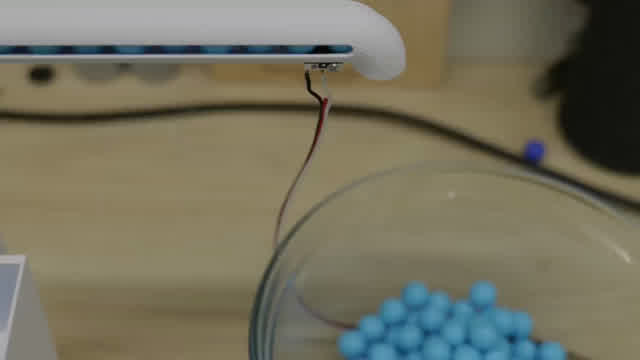
video_analsys/frames/0099.jpg
