hcen1997/pixel-bean/video_analsys/frames/0100.jpg

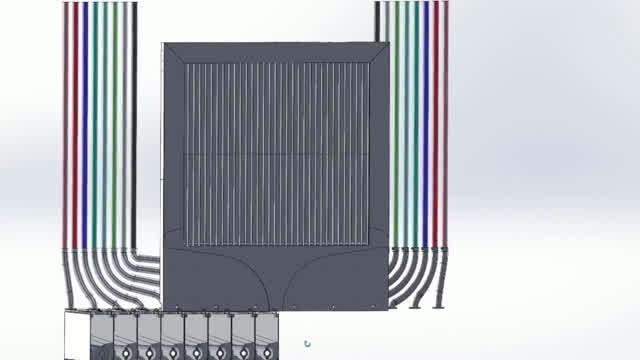
video_analsys/frames/0100.jpg
