hcen1997/pixel-bean/video_analsys/frames/0101.jpg

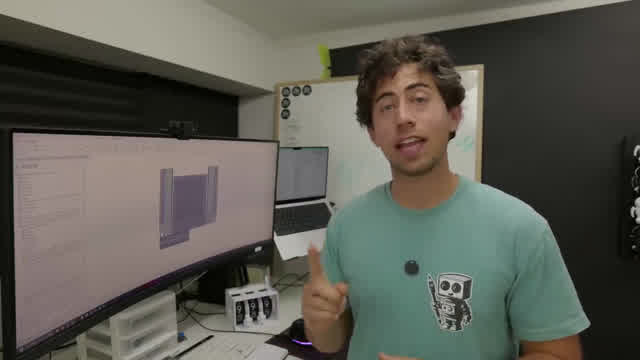
video_analsys/frames/0101.jpg
