hcen1997/pixel-bean/video_analsys/frames/0102.jpg

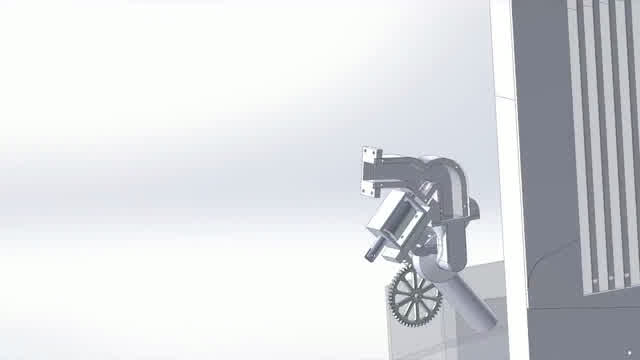
video_analsys/frames/0102.jpg
