hcen1997/pixel-bean/video_analsys/frames/0103.jpg

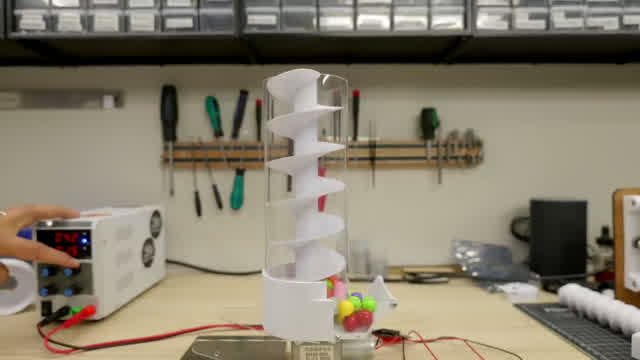
video_analsys/frames/0103.jpg
