hcen1997/pixel-bean/video_analsys/frames/0104.jpg

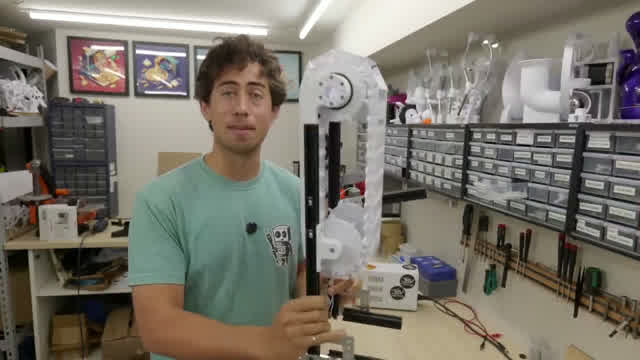
video_analsys/frames/0104.jpg
