hcen1997/pixel-bean/video_analsys/frames/0105.jpg

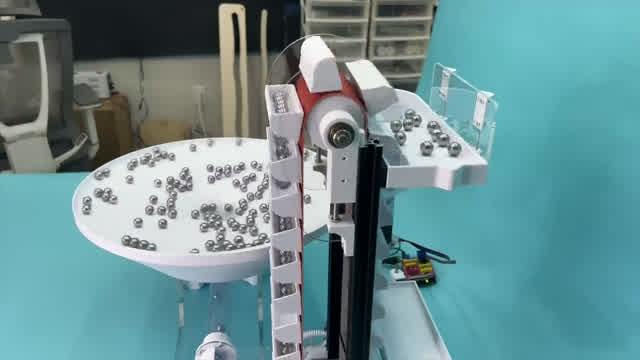
video_analsys/frames/0105.jpg
