hcen1997/pixel-bean/video_analsys/frames/0106.jpg

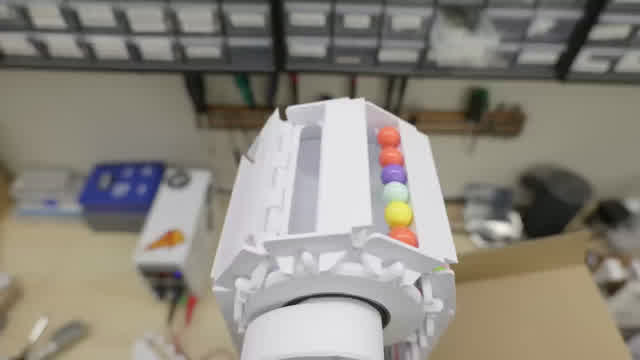
video_analsys/frames/0106.jpg
