hcen1997/pixel-bean/video_analsys/frames/0107.jpg

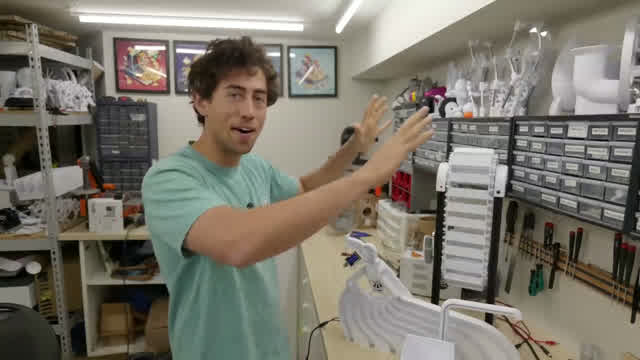
video_analsys/frames/0107.jpg
