hcen1997/pixel-bean/video_analsys/frames/0108.jpg

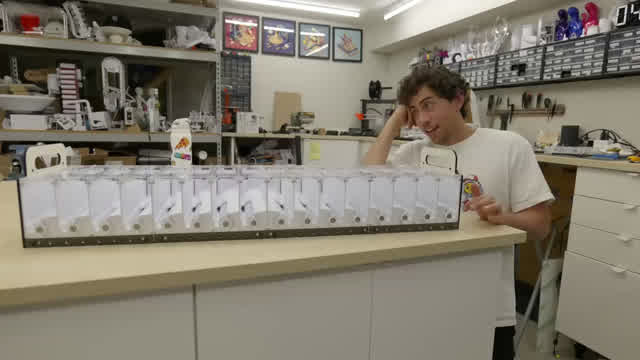
video_analsys/frames/0108.jpg
