hcen1997/pixel-bean/video_analsys/frames/0109.jpg

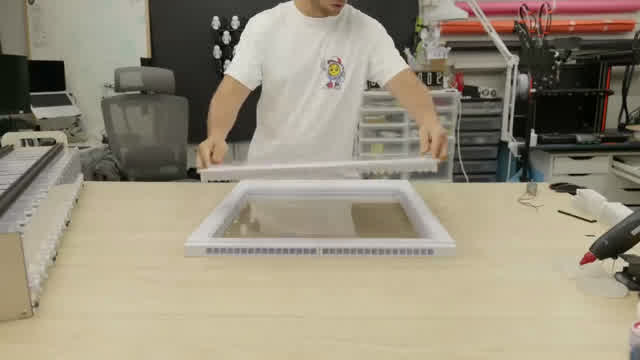
video_analsys/frames/0109.jpg
