hcen1997/pixel-bean/video_analsys/frames/0110.jpg

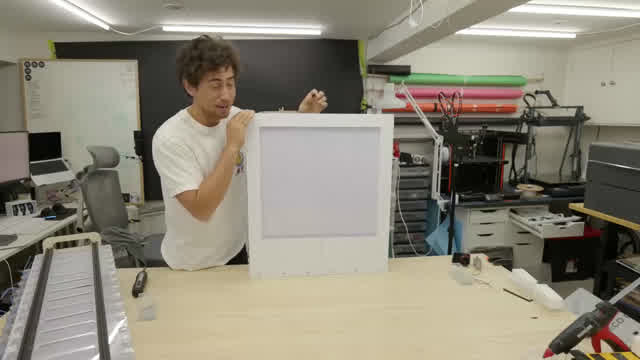
video_analsys/frames/0110.jpg
