hcen1997/pixel-bean/video_analsys/frames/0111.jpg

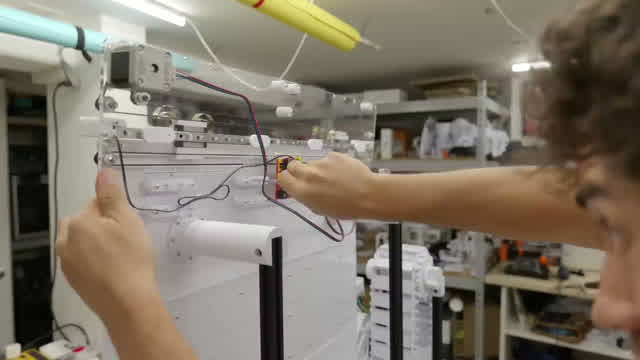
video_analsys/frames/0111.jpg
