hcen1997/pixel-bean/video_analsys/frames/0112.jpg

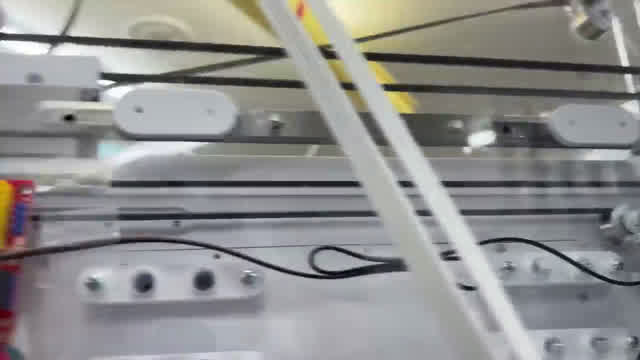
video_analsys/frames/0112.jpg
