hcen1997/pixel-bean/video_analsys/frames/0113.jpg

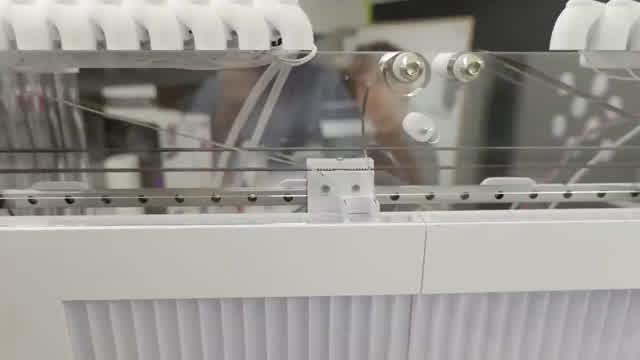
video_analsys/frames/0113.jpg
