hcen1997/pixel-bean/video_analsys/frames/0114.jpg

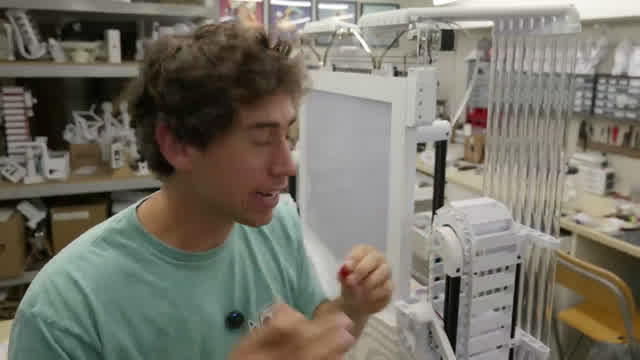
video_analsys/frames/0114.jpg
