hcen1997/pixel-bean/video_analsys/frames/0115.jpg

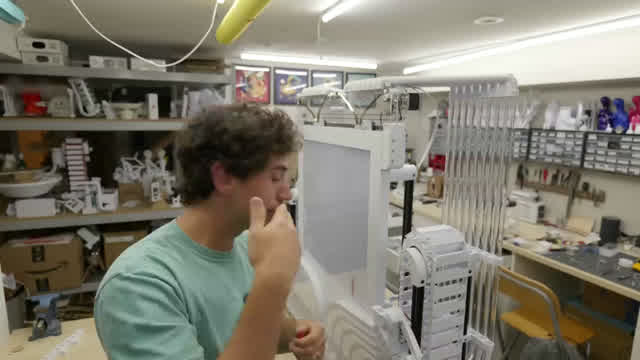
video_analsys/frames/0115.jpg
