hcen1997/pixel-bean/video_analsys/frames/0116.jpg

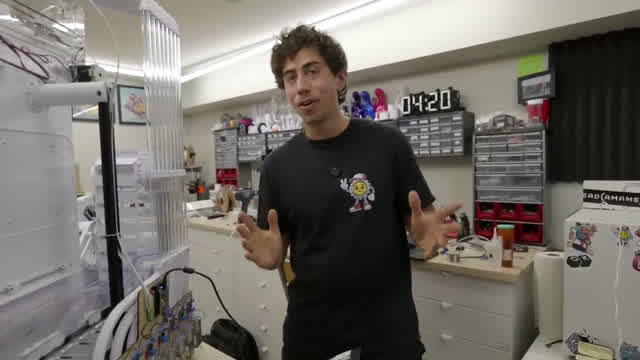
video_analsys/frames/0116.jpg
