hcen1997/pixel-bean/video_analsys/frames/0117.jpg

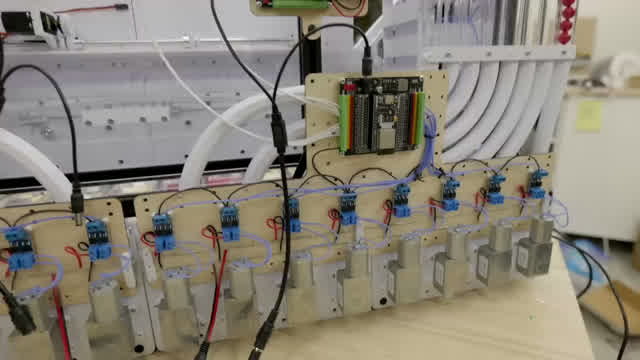
video_analsys/frames/0117.jpg
