hcen1997/pixel-bean/video_analsys/frames/0118.jpg

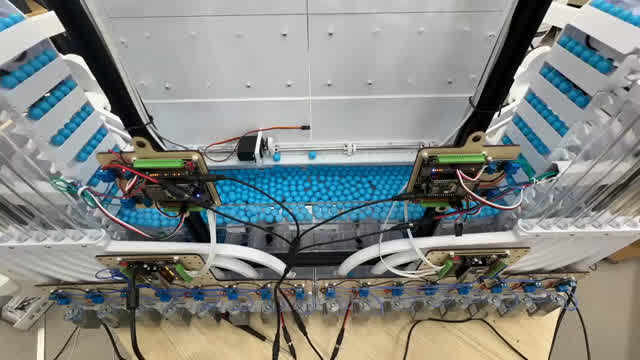
video_analsys/frames/0118.jpg
