hcen1997/pixel-bean/video_analsys/frames/0119.jpg

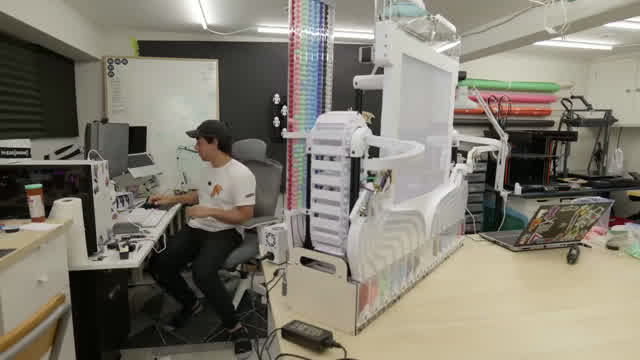
video_analsys/frames/0119.jpg
