hcen1997/pixel-bean/video_analsys/frames/0120.jpg

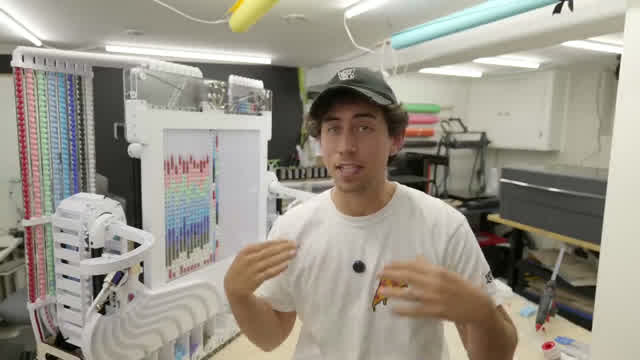
video_analsys/frames/0120.jpg
