hcen1997/pixel-bean/video_analsys/frames/0121.jpg

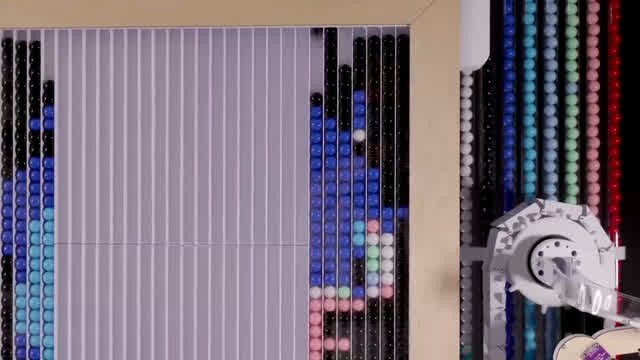
video_analsys/frames/0121.jpg
