hcen1997/pixel-bean/video_analsys/frames/0122.jpg

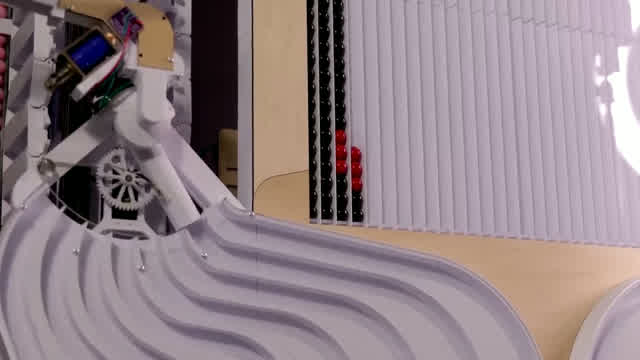
video_analsys/frames/0122.jpg
