hcen1997/pixel-bean/video_analsys/frames/0123.jpg

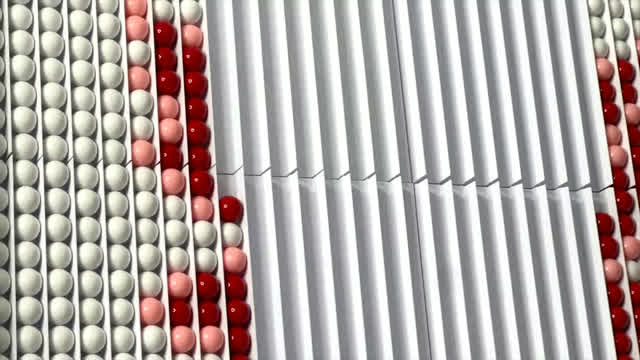
video_analsys/frames/0123.jpg
