hcen1997/pixel-bean/video_analsys/frames/0124.jpg

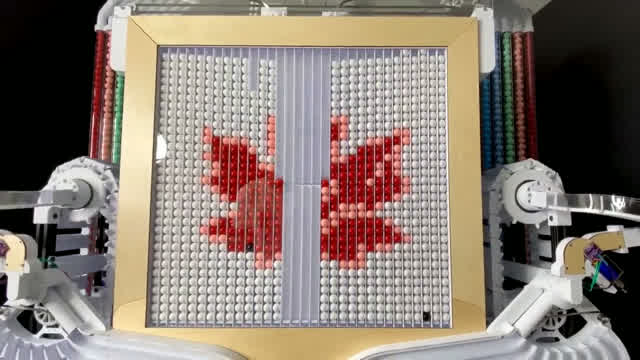
video_analsys/frames/0124.jpg
