hcen1997/pixel-bean/video_analsys/frames/0125.jpg

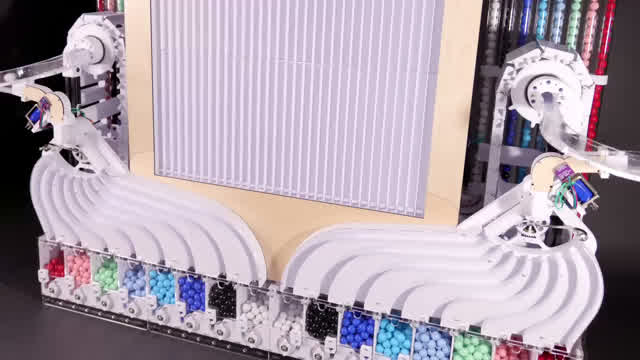
video_analsys/frames/0125.jpg
