hcen1997/pixel-bean/video_analsys/frames/0126.jpg

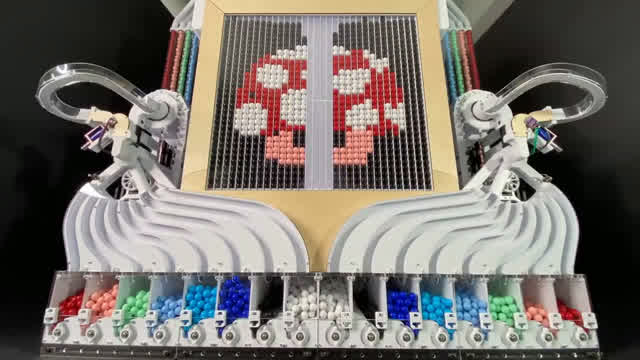
video_analsys/frames/0126.jpg
