hcen1997/pixel-bean/video_analsys/frames/0127.jpg

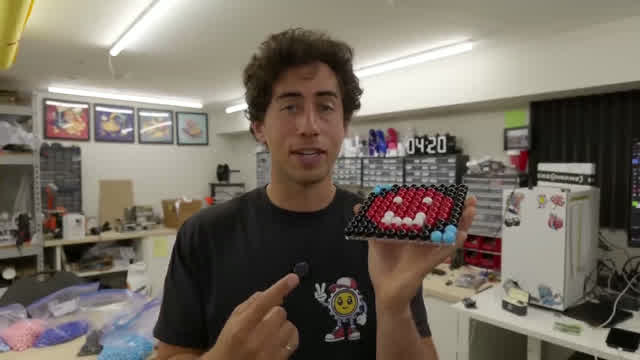
video_analsys/frames/0127.jpg
