hcen1997/pixel-bean/【大鱼DIY】雕绘仪 EP V3.0 全套资料/【大鱼DIY】雕绘仪 EP V3.0.jpg

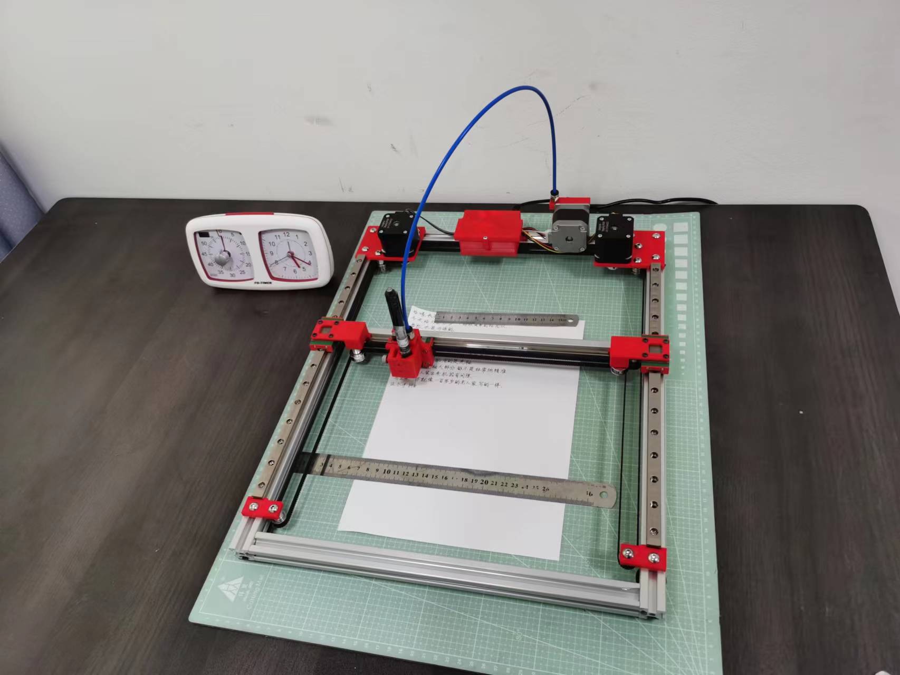
【大鱼DIY】雕绘仪 EP V3.0 全套资料/【大鱼DIY】雕绘仪 EP V3.0.jpg
