hcen1997/pixel-bean/【大鱼DIY】雕绘仪 EP V3.0 全套资料/皮带固定孔距.png

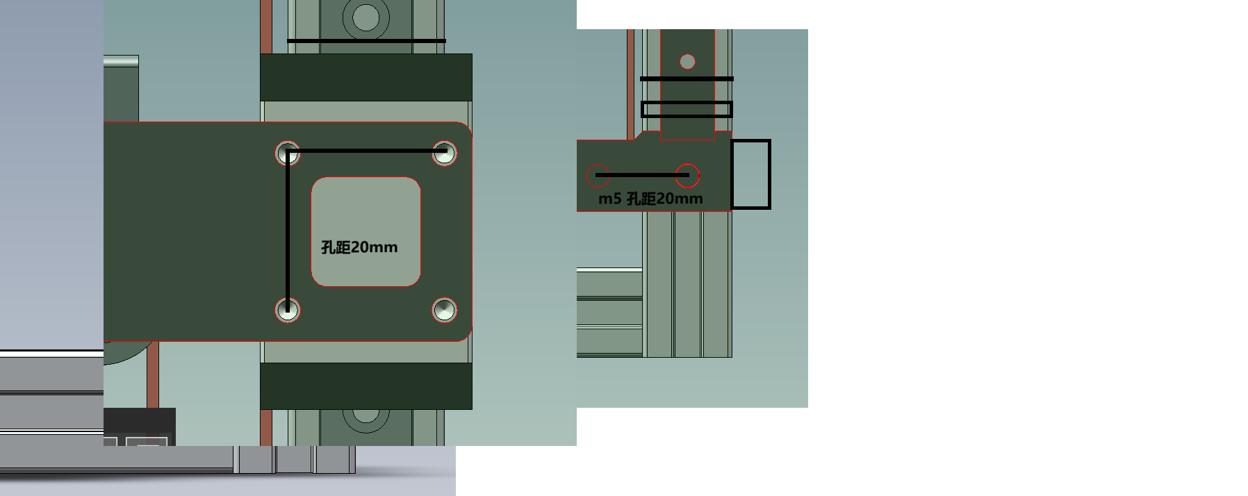
【大鱼DIY】雕绘仪 EP V3.0 全套资料/皮带固定孔距.png
