hcen1997/pixel-bean/【大鱼DIY】雕绘仪 EP V3.0 全套资料/STP格式零件/主板盖子.STEP

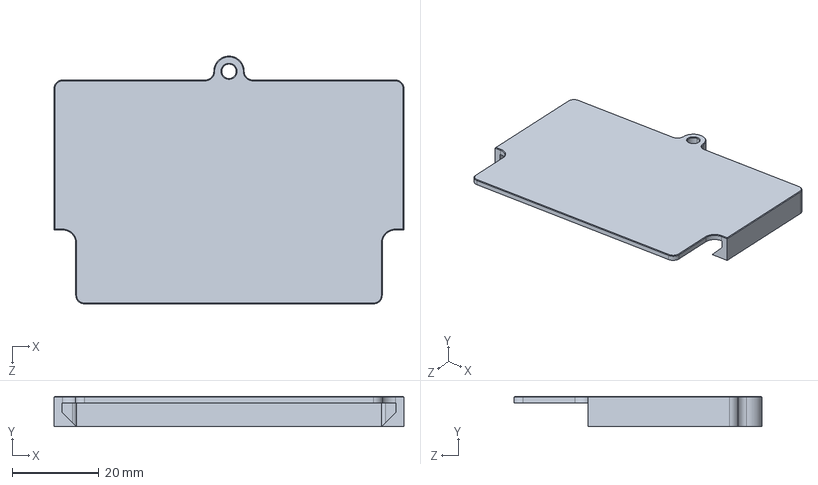
[picture p158: CAD file, 2026-03-05]
【大鱼DIY】雕绘仪 EP V3.0 全套资料/STP格式零件/主板盖子.STEP
80.5 x 7.00 x 57.0 mm
