hcen1997/pixel-bean/【大鱼DIY】雕绘仪 EP V3.0 全套资料/STP格式零件/主板盒子.STEP

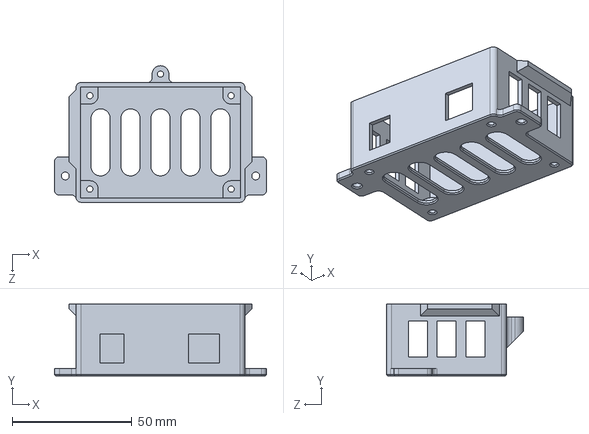
[picture p159: CAD file, 2026-03-05]
【大鱼DIY】雕绘仪 EP V3.0 全套资料/STP格式零件/主板盒子.STEP
88.5 x 30.0 x 57.0 mm
